edwardschmitz/sigcore-uc/docs/Drawings/sketches/4-20mA-output-loop.png

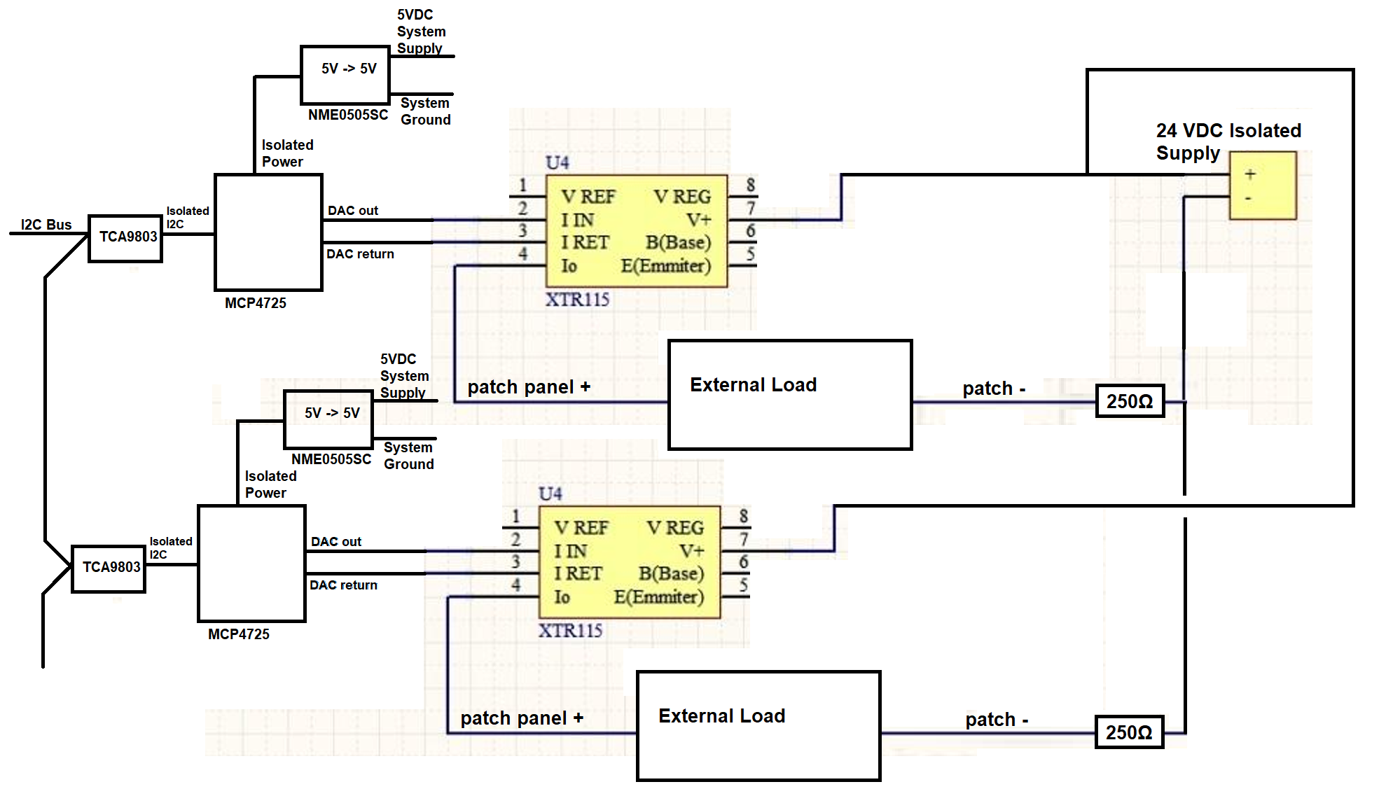
docs/Drawings/sketches/4-20mA-output-loop.png
