edwardschmitz/sigcore-uc/docs/Drawings/sketches/analog-in-conditinoer-select.png

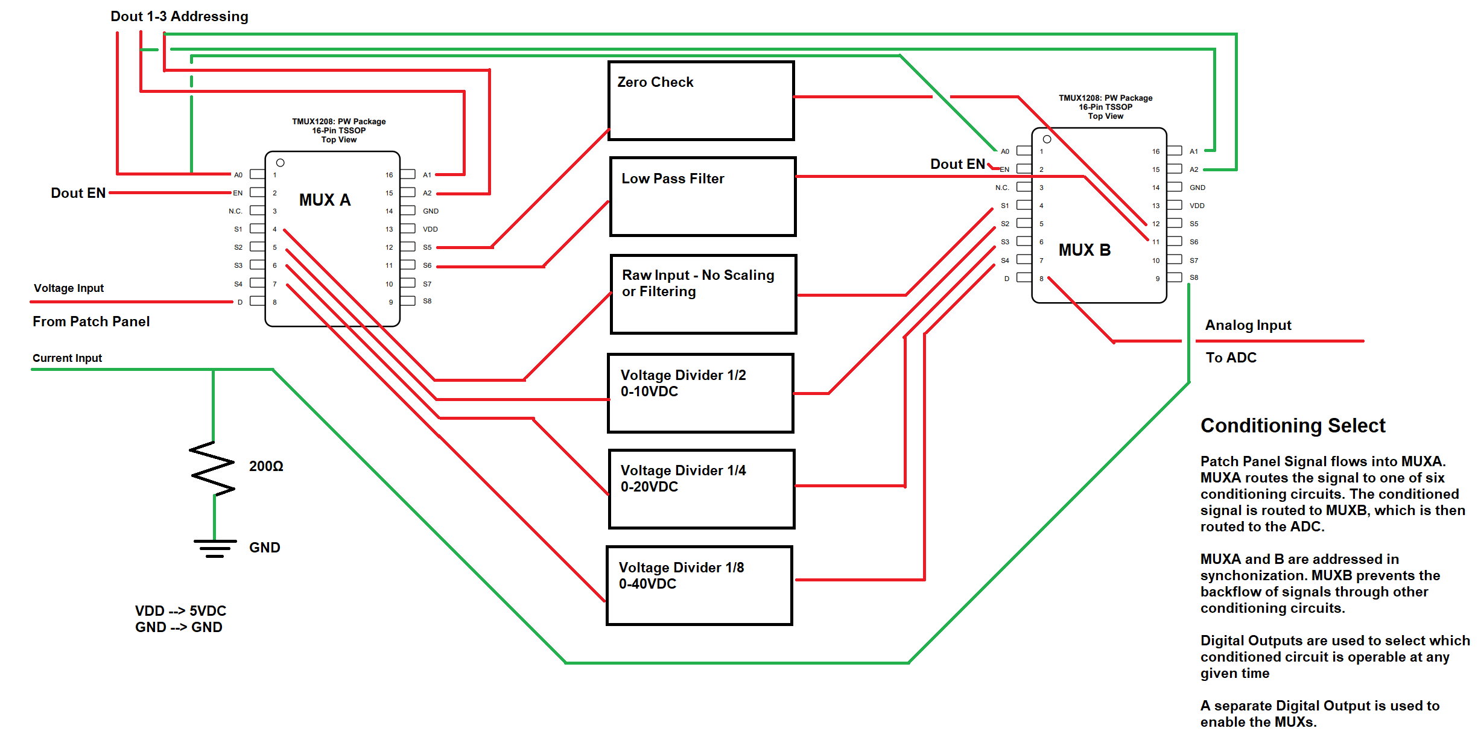
docs/Drawings/sketches/analog-in-conditinoer-select.png
