edwardschmitz/sigcore-uc/docs/Drawings/sketches/current-sensing.png

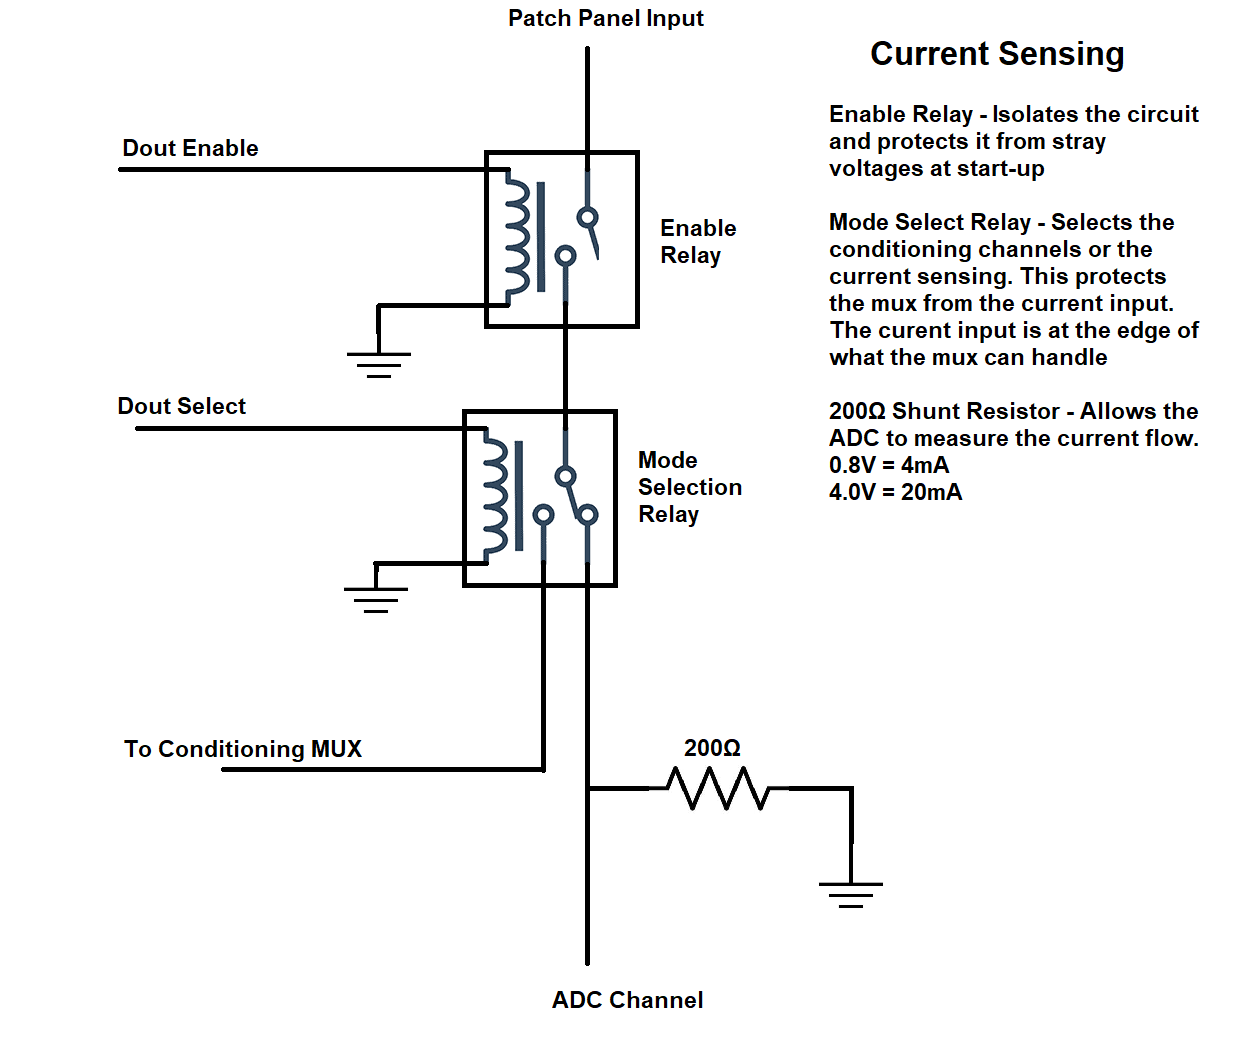
docs/Drawings/sketches/current-sensing.png
