edwardschmitz/sigcore-uc/docs/Drawings/sketches/Relay Driver.png

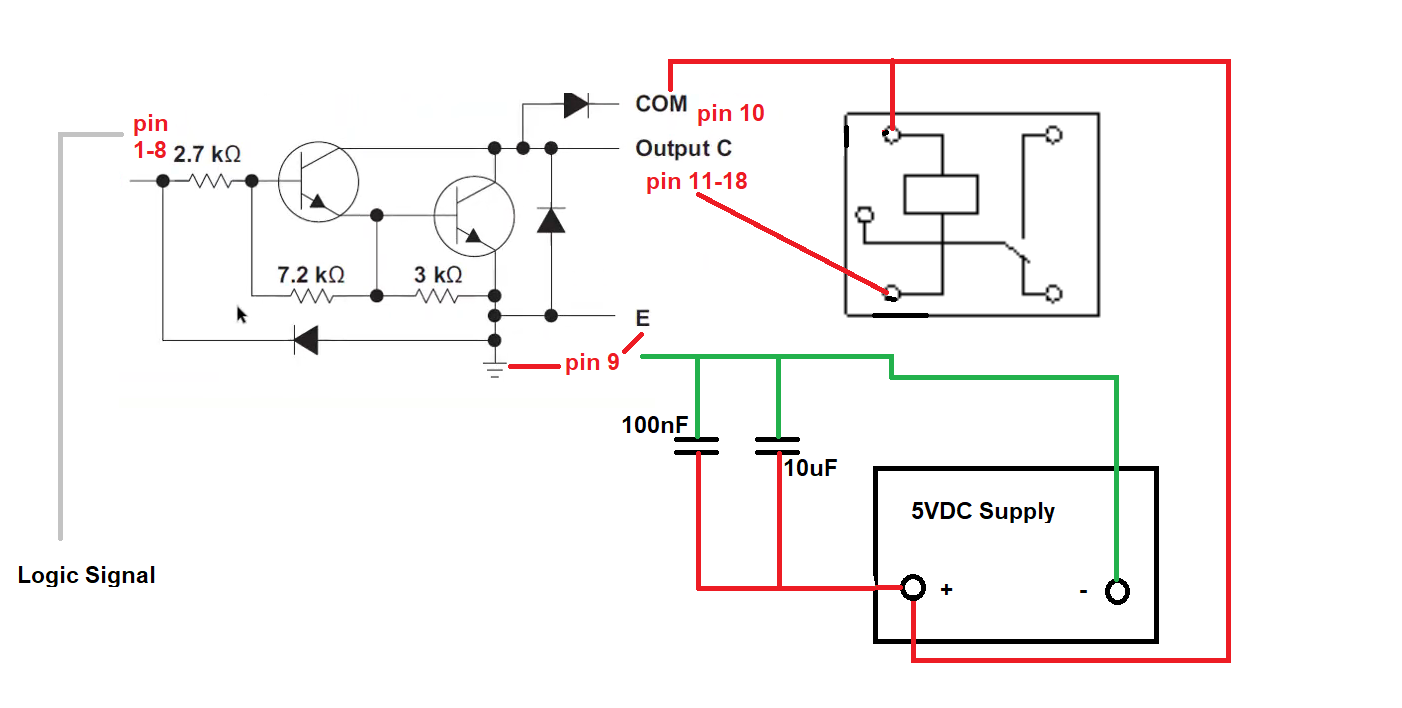
docs/Drawings/sketches/Relay Driver.png
