edwardschmitz/sigcore-uc/docs/Drawings/sketches/relay-circuit.png

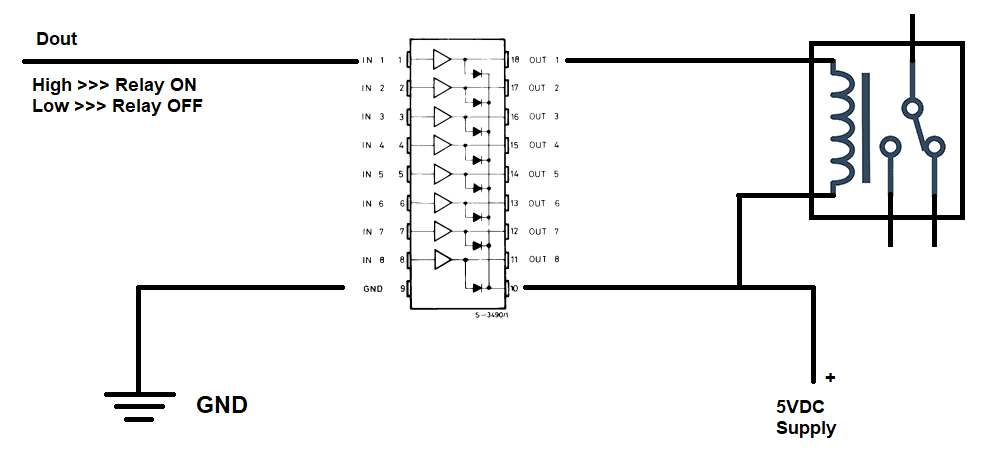
docs/Drawings/sketches/relay-circuit.png
