edwardschmitz/sigcore-uc/docs/Drawings/sketches/universal-analog-output.png

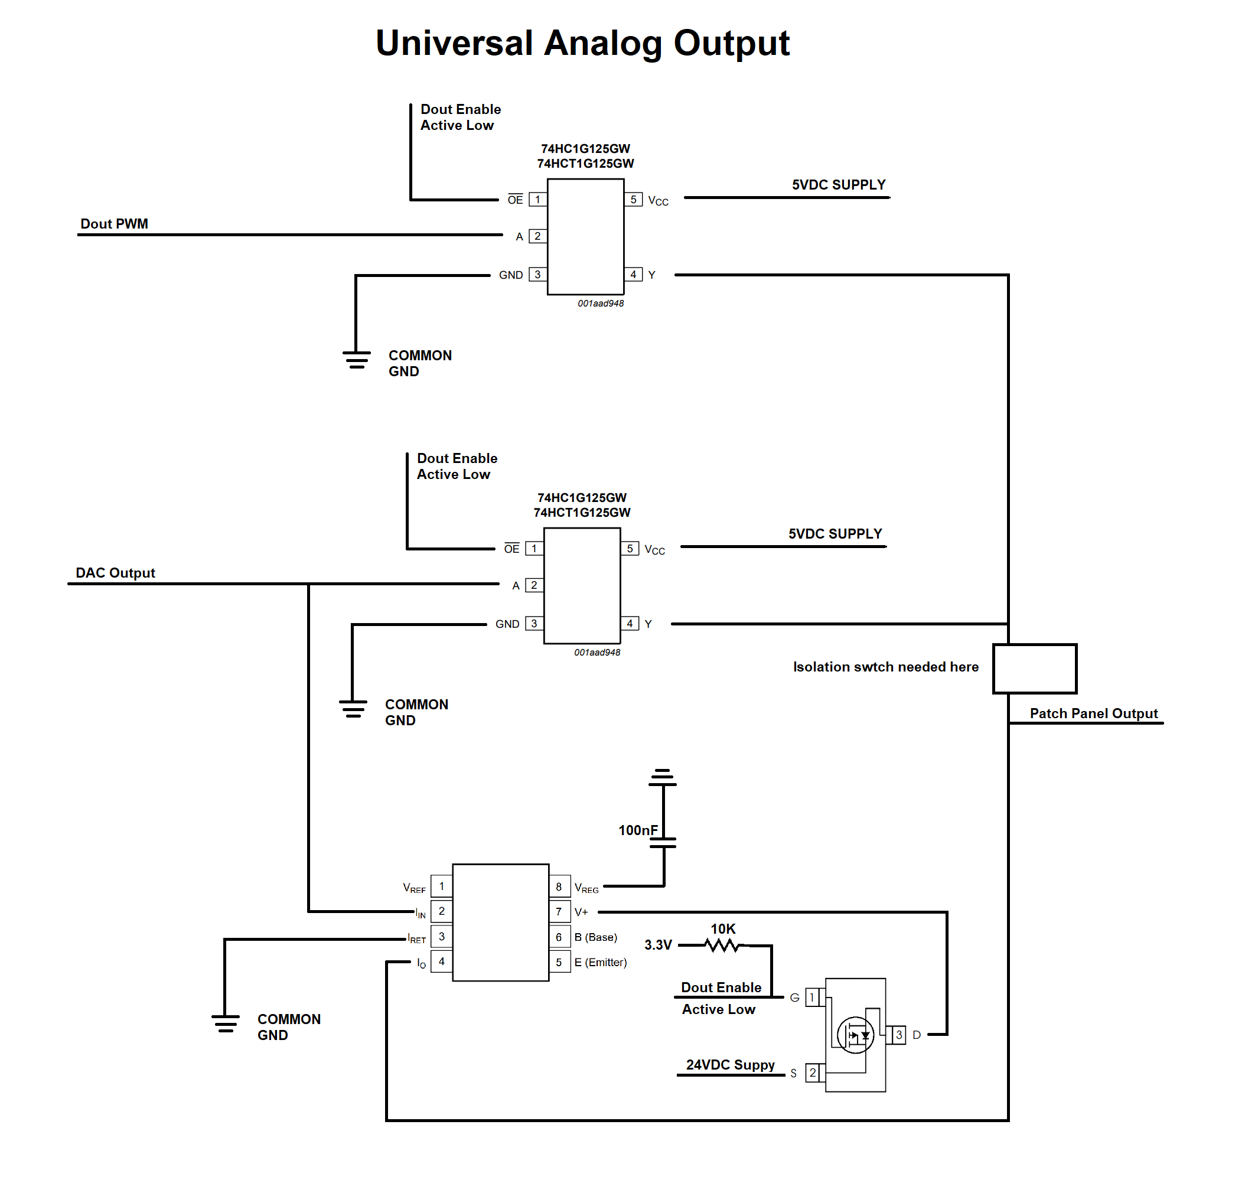
docs/Drawings/sketches/universal-analog-output.png
