edwardschmitz/sigcore-uc/docs/Drawings/sketches/universal-digital-input.png

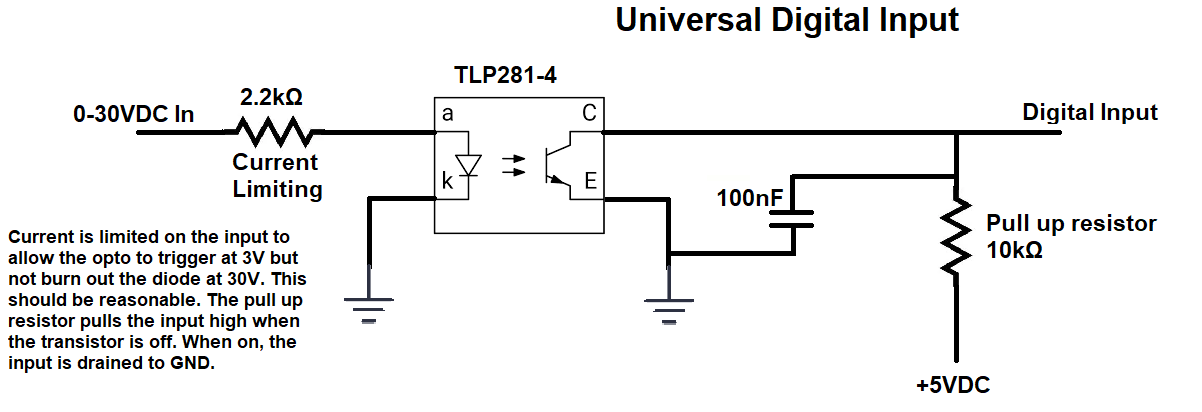
docs/Drawings/sketches/universal-digital-input.png
