edwardschmitz/sigcore-uc/docs/Images/1000008632.jpg

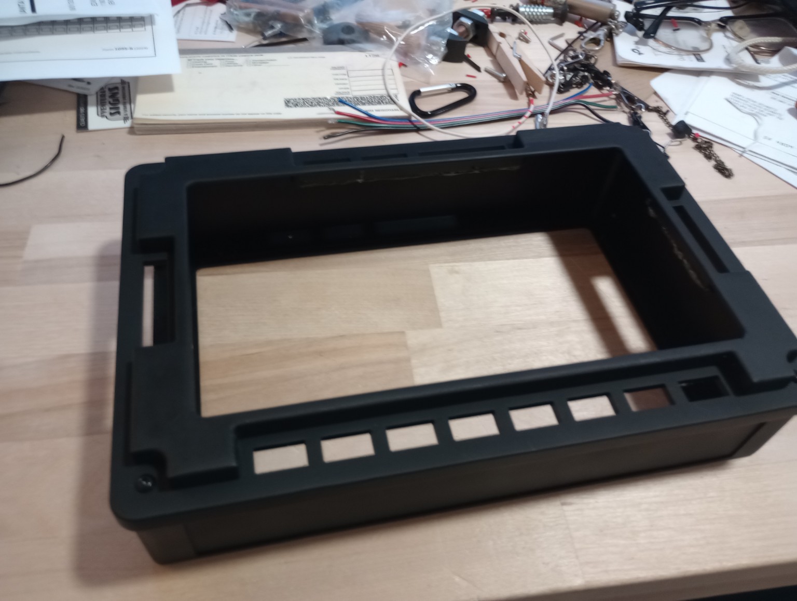
docs/Images/1000008632.jpg
