edwardschmitz/sigcore-uc/docs/Images/1000009032.jpg

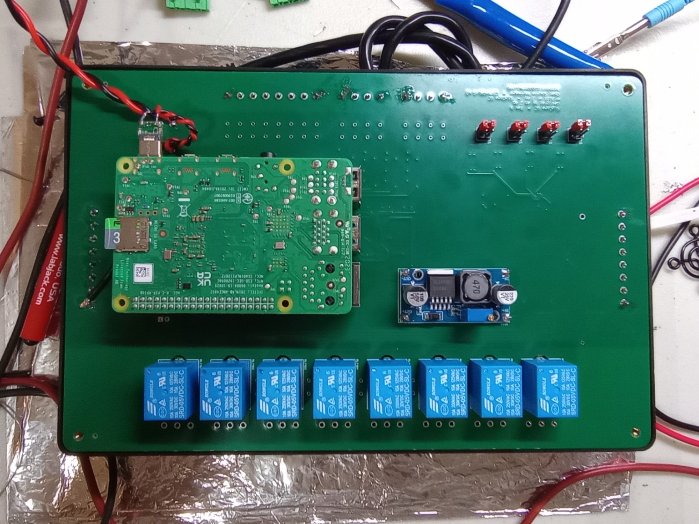
docs/Images/1000009032.jpg
