edwardschmitz/sigcore-uc/docs/Images/1000009033.jpg

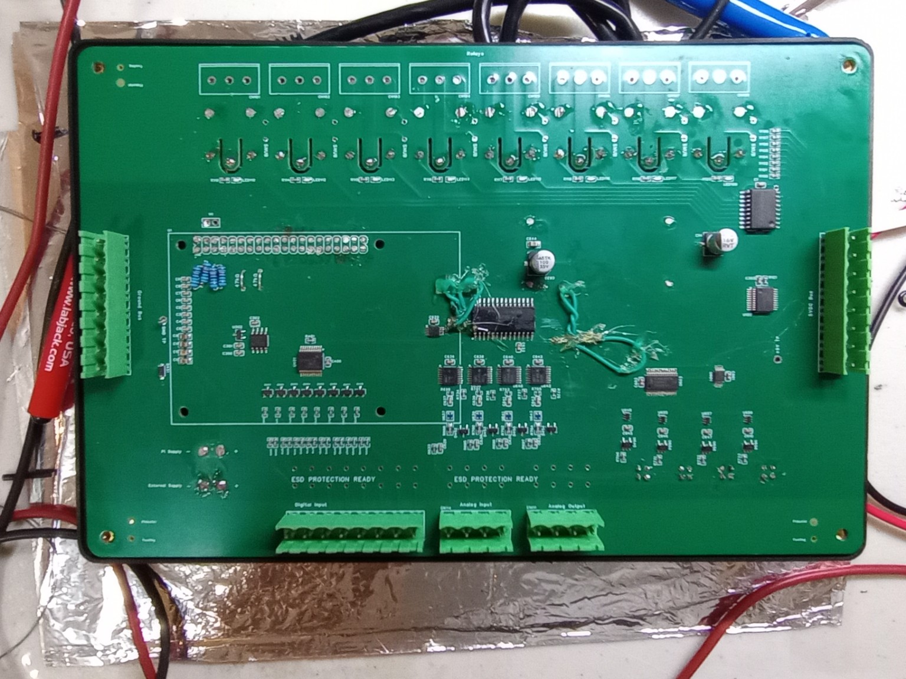
docs/Images/1000009033.jpg
