edwardschmitz/sigcore-uc/docs/Images/abstract-circuit.png

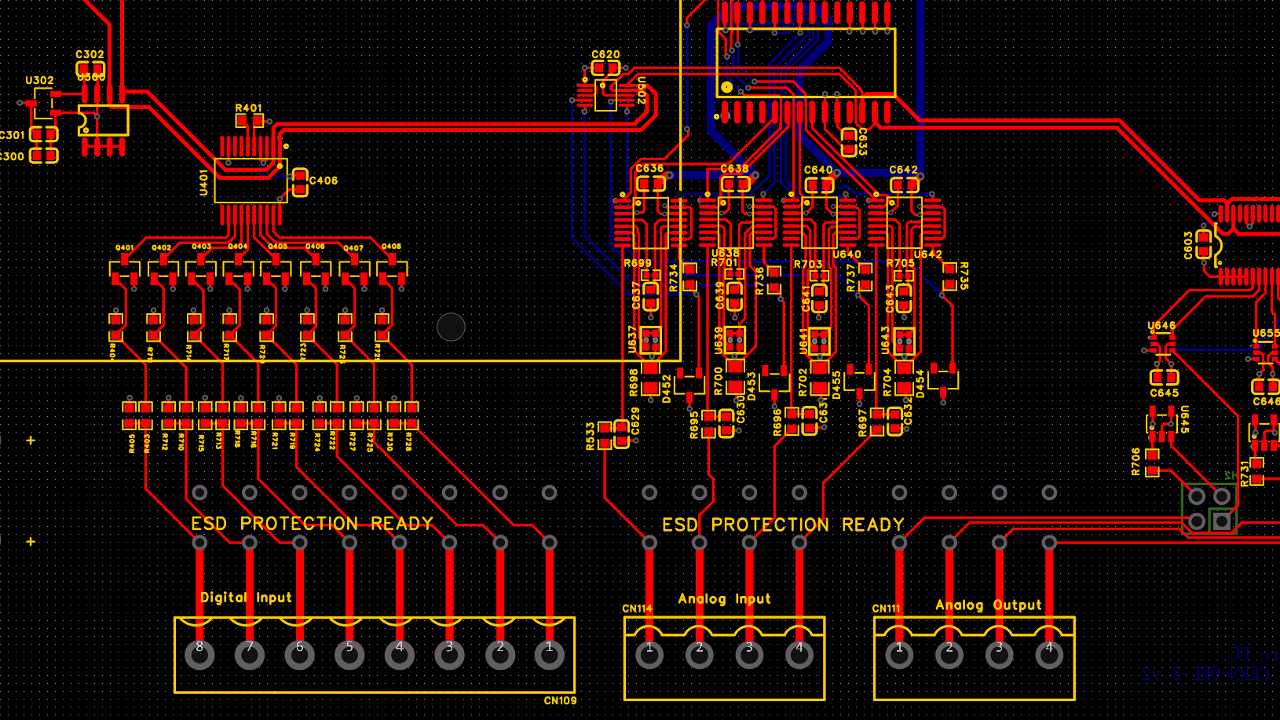
docs/Images/abstract-circuit.png
