edwardschmitz/sigcore-uc/docs/Images/analog-properties.png

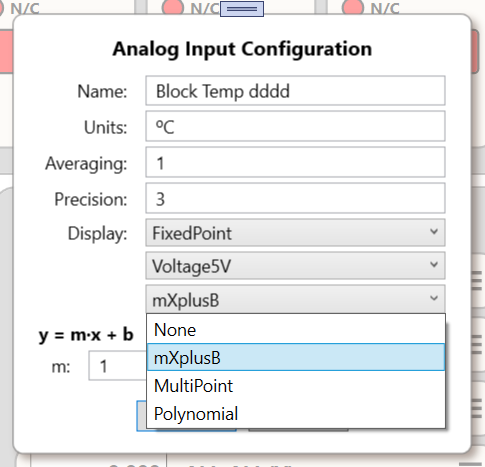
docs/Images/analog-properties.png
