edwardschmitz/sigcore-uc/docs/Images/angle-view.jpg

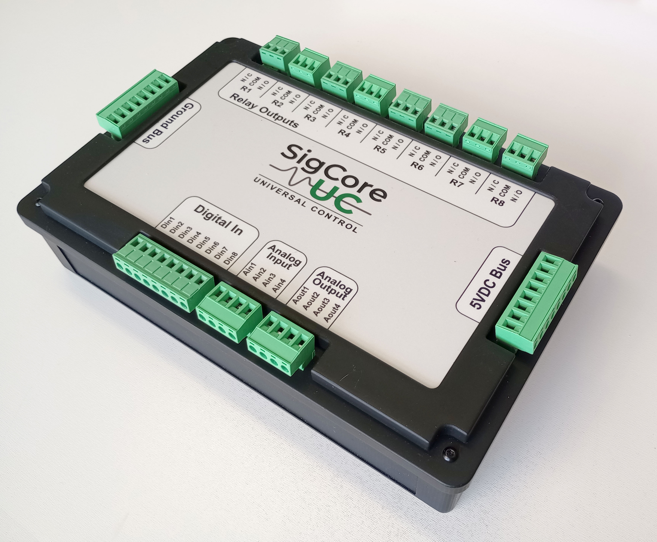
docs/Images/angle-view.jpg
