edwardschmitz/sigcore-uc/docs/Images/Board_v1_2025-Sep-24_08-21-38PM-000_CustomizedView15039400652.png

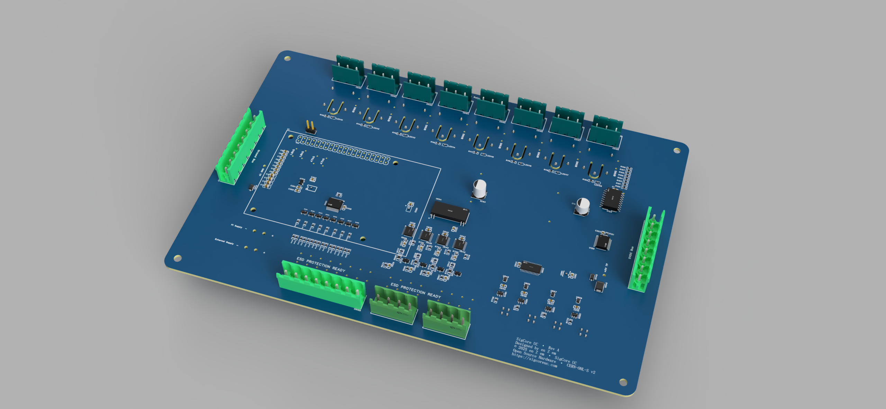
docs/Images/Board_v1_2025-Sep-24_08-21-38PM-000_CustomizedView15039400652.png
