edwardschmitz/sigcore-uc/docs/Images/breakout board.jpg

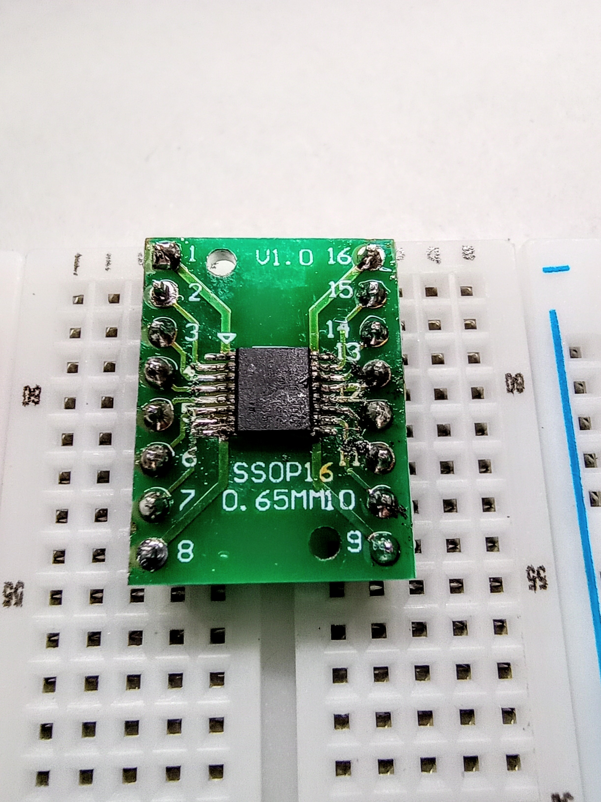
docs/Images/breakout board.jpg
