edwardschmitz/sigcore-uc/docs/Images/circuit-board.png

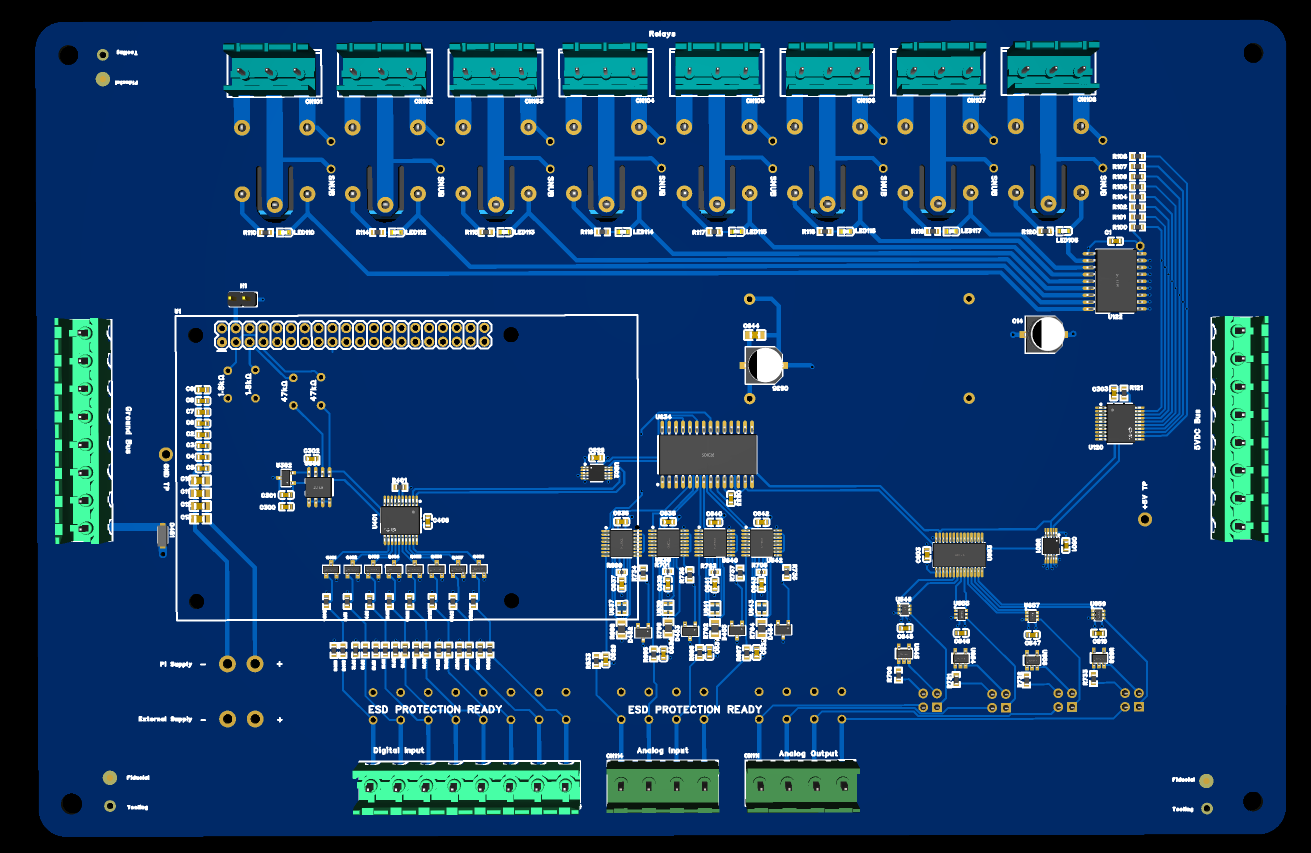
docs/Images/circuit-board.png
