edwardschmitz/sigcore-uc/docs/Images/control-panel-software.png

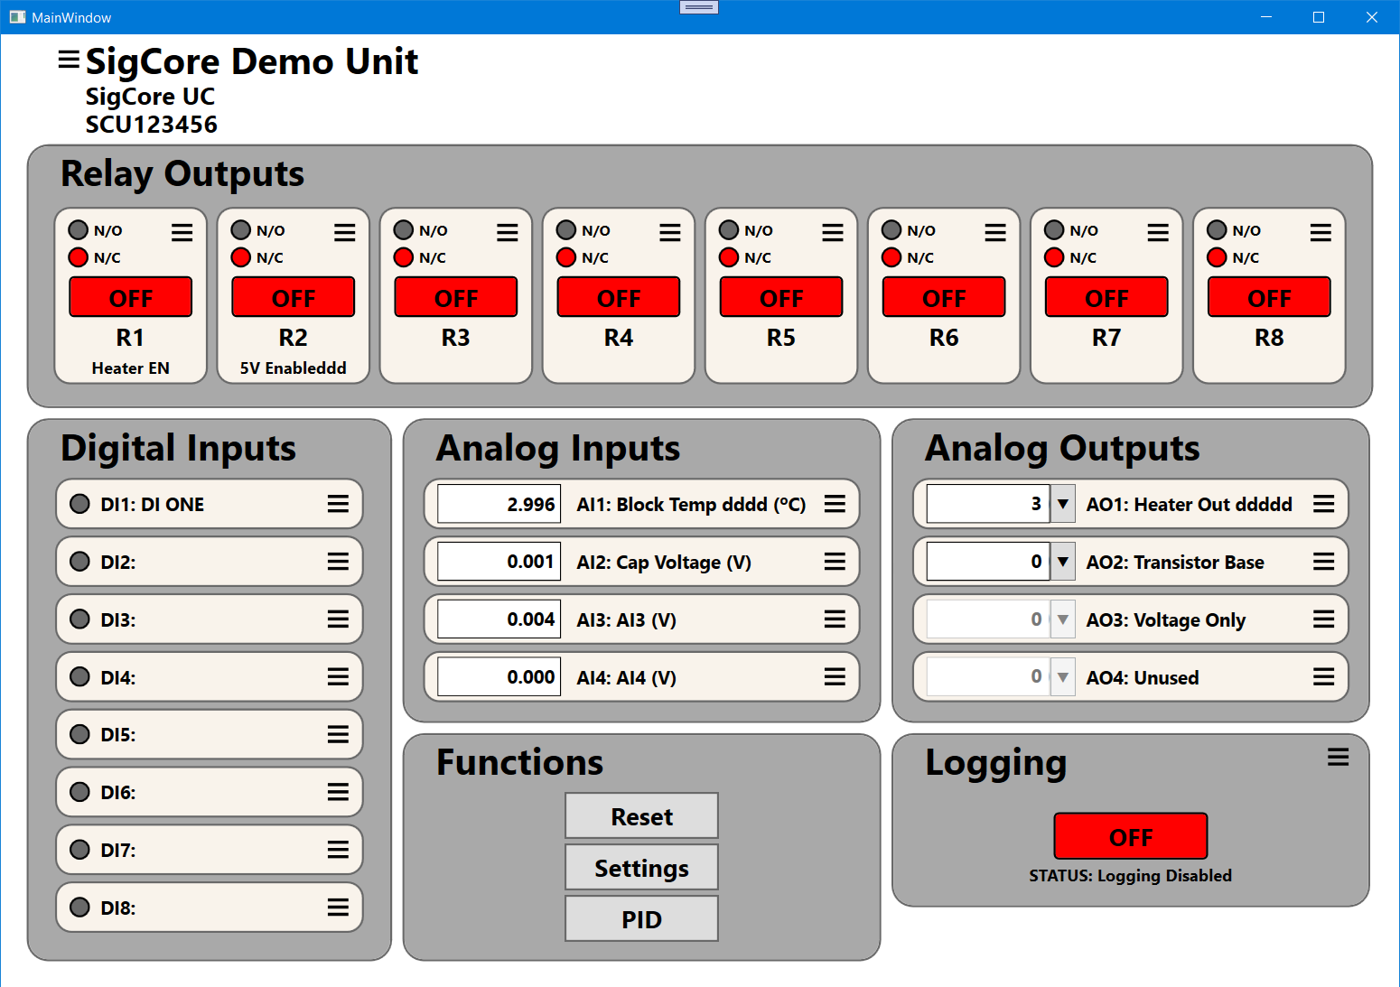
docs/Images/control-panel-software.png
