edwardschmitz/sigcore-uc/docs/Images/enclosure-rendering.png

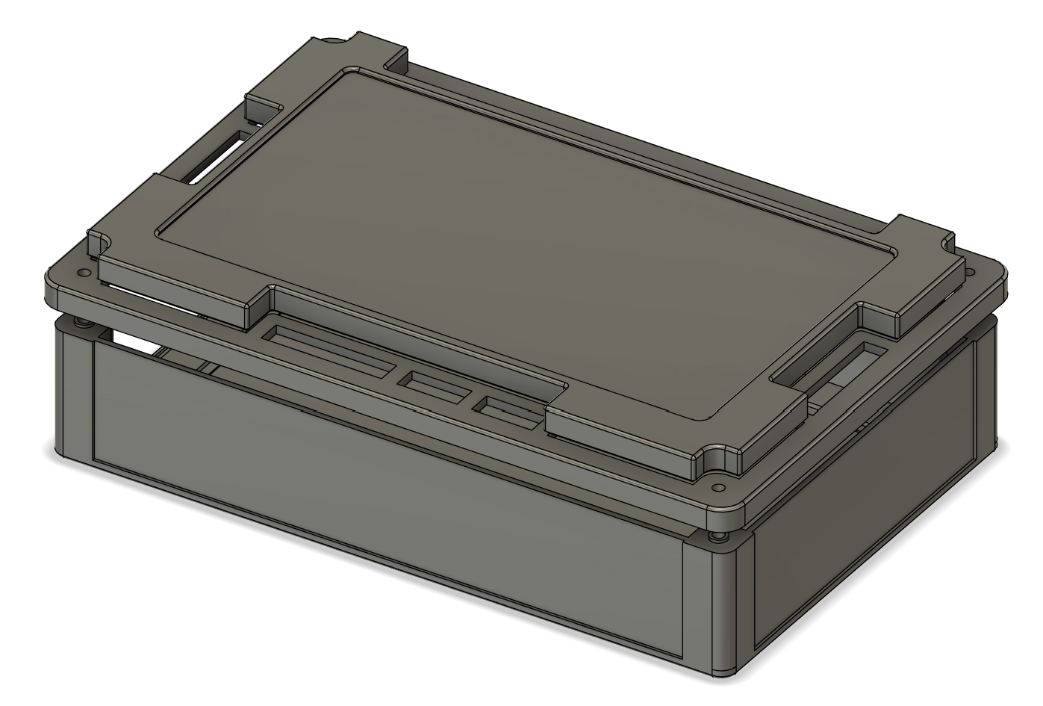
docs/Images/enclosure-rendering.png
