edwardschmitz/sigcore-uc/docs/Images/front-angle.jpg

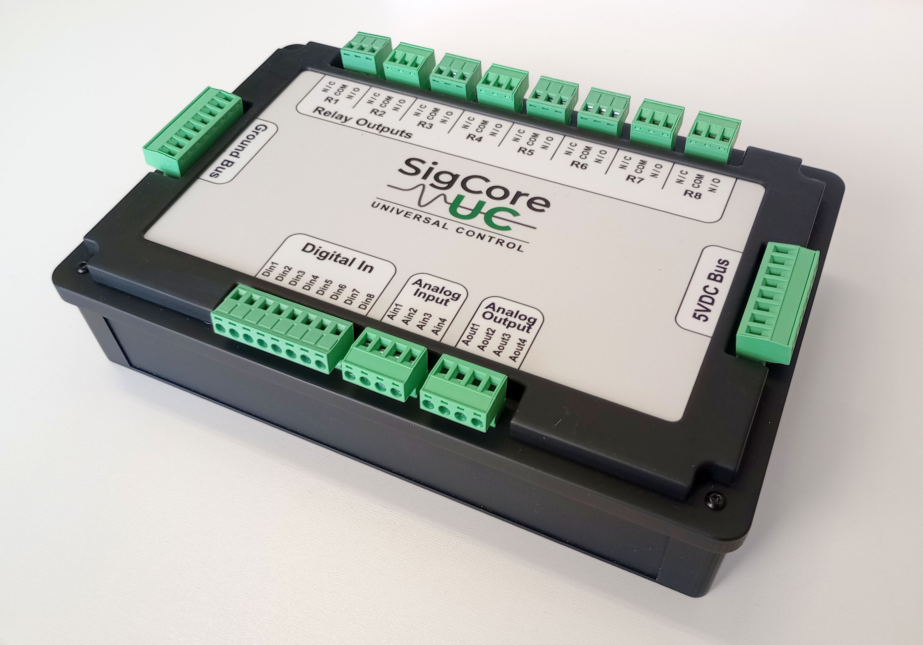
docs/Images/front-angle.jpg
