edwardschmitz/sigcore-uc/docs/Images/front.jpg

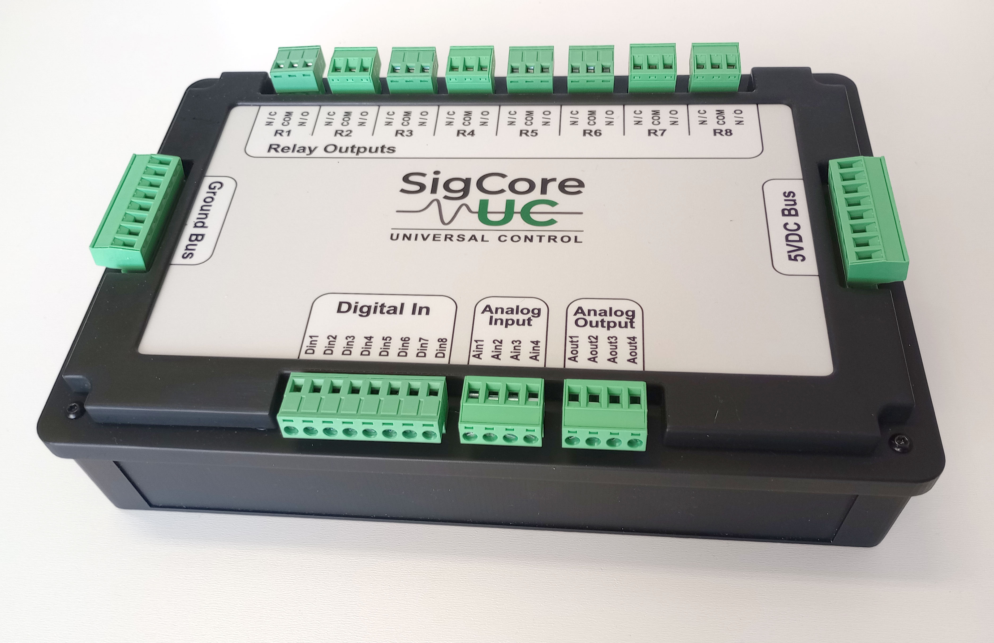
docs/Images/front.jpg
