edwardschmitz/sigcore-uc/docs/Images/hackster-article.jpg

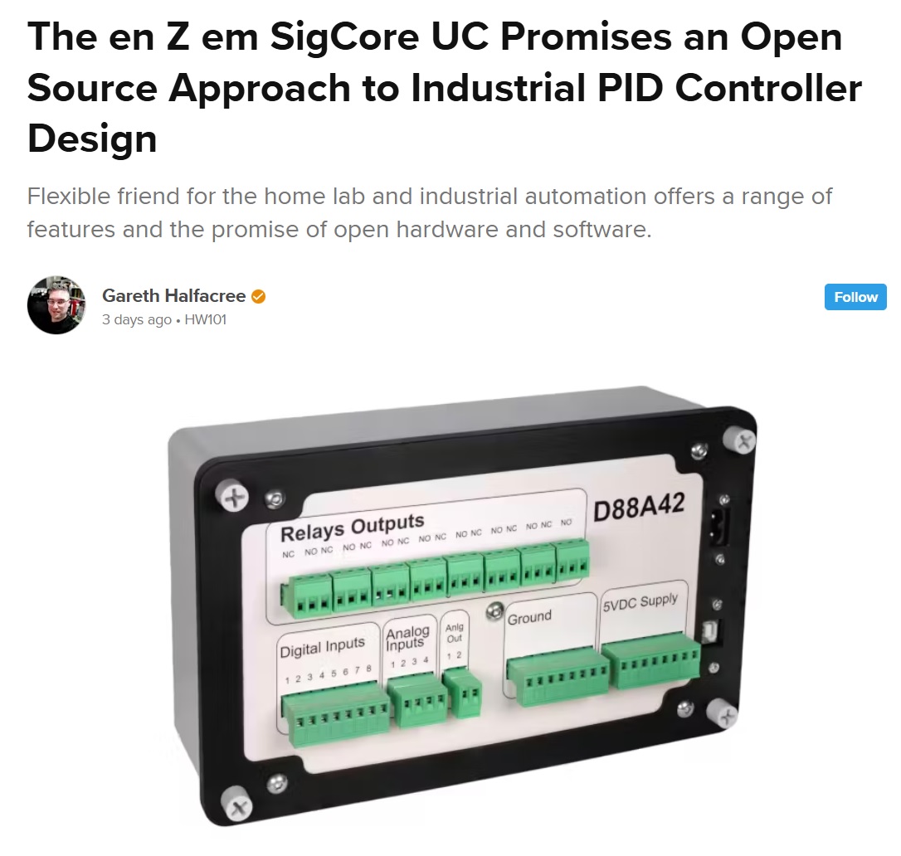
docs/Images/hackster-article.jpg
