edwardschmitz/sigcore-uc/docs/Images/IMG_20250718_141825615.jpg

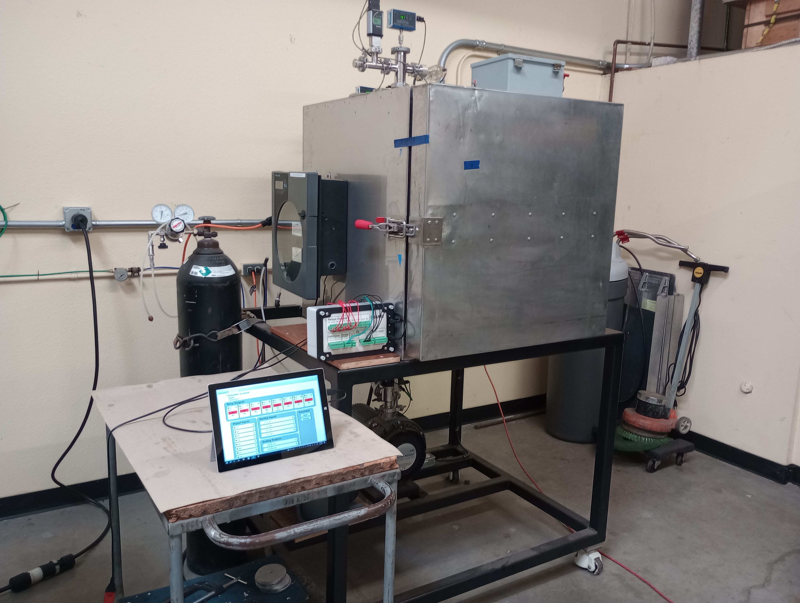
docs/Images/IMG_20250718_141825615.jpg
