edwardschmitz/sigcore-uc/docs/Images/IMG_20250718_141832880.jpg

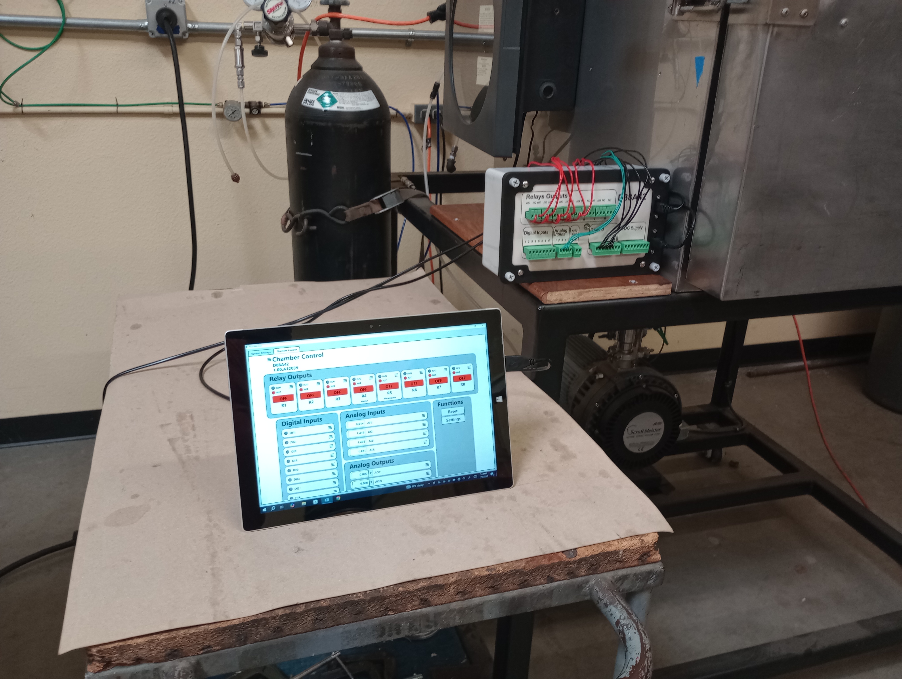
docs/Images/IMG_20250718_141832880.jpg
