edwardschmitz/sigcore-uc/docs/Images/IMG_20250718_141838460.jpg

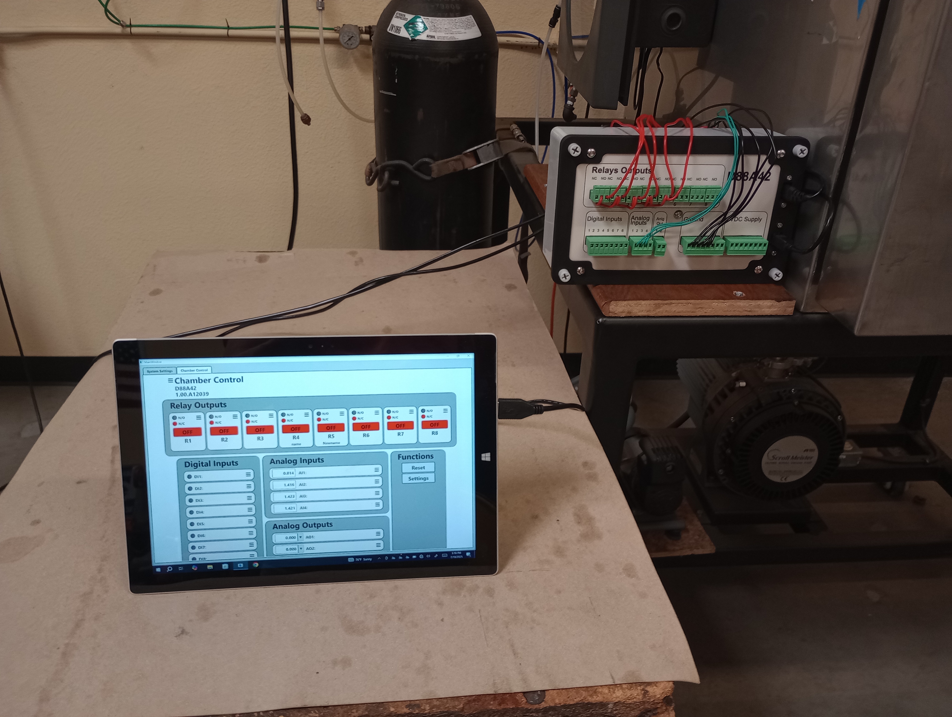
docs/Images/IMG_20250718_141838460.jpg
