edwardschmitz/sigcore-uc/docs/Images/IMG_20250718_141848650.jpg

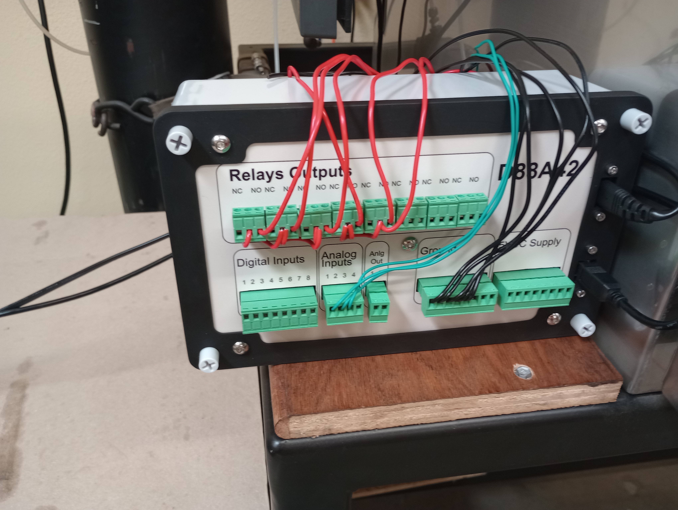
docs/Images/IMG_20250718_141848650.jpg
