edwardschmitz/sigcore-uc/docs/Images/IMG_20250718_141900908.jpg

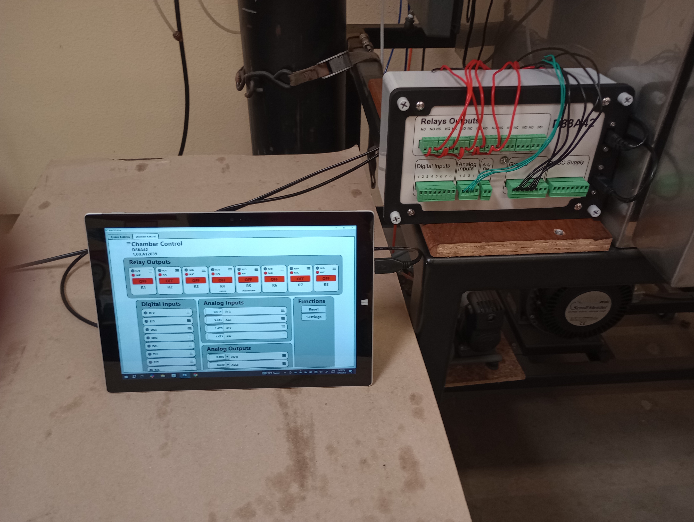
docs/Images/IMG_20250718_141900908.jpg
