edwardschmitz/sigcore-uc/docs/Images/IMG_20250718_143222500.jpg

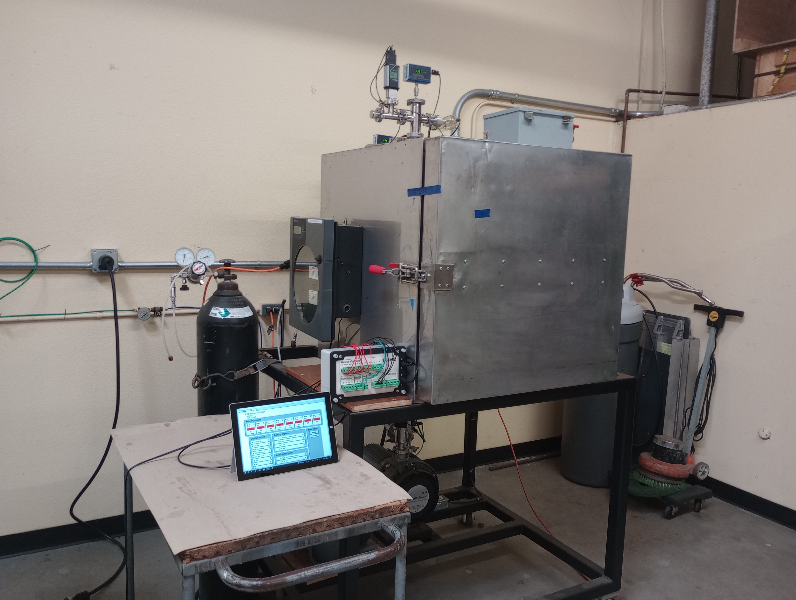
docs/Images/IMG_20250718_143222500.jpg
