edwardschmitz/sigcore-uc/docs/Images/IMG_20250718_143229647.jpg

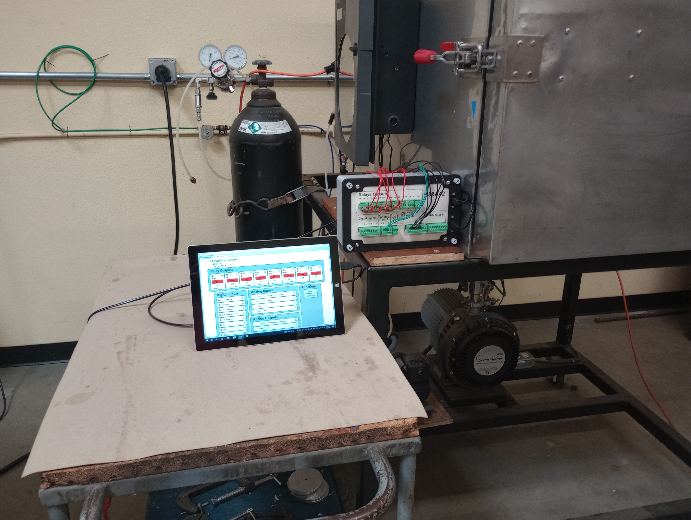
docs/Images/IMG_20250718_143229647.jpg
