edwardschmitz/sigcore-uc/docs/Images/IMG_20250718_143235979.jpg

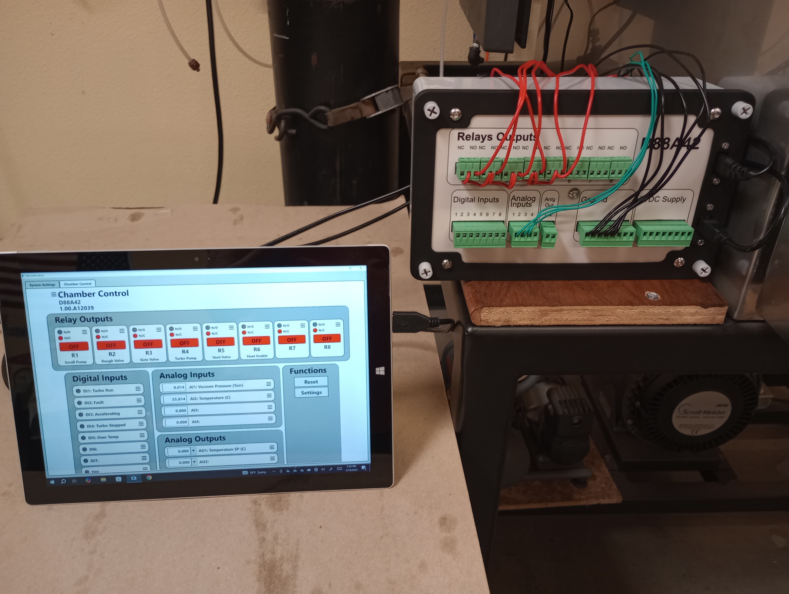
docs/Images/IMG_20250718_143235979.jpg
