edwardschmitz/sigcore-uc/docs/Images/IMG_20250718_143255635.jpg

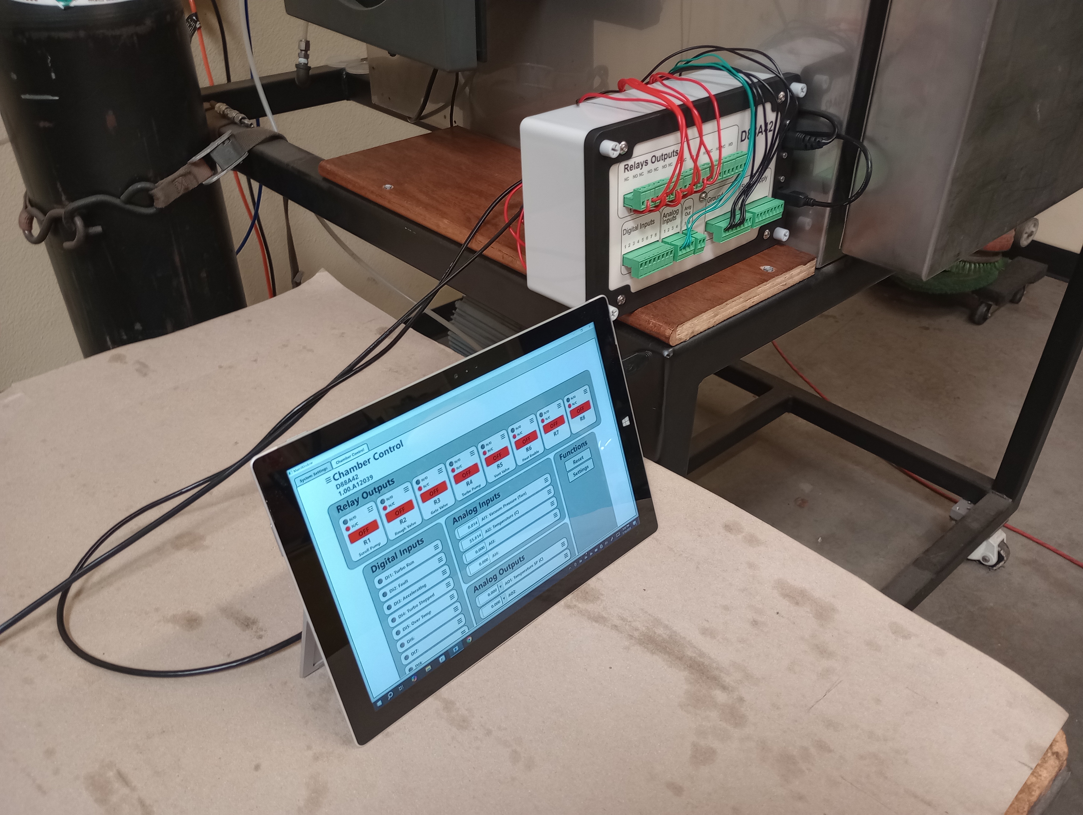
docs/Images/IMG_20250718_143255635.jpg
