edwardschmitz/sigcore-uc/docs/Images/IMG_20250718_143305820.jpg

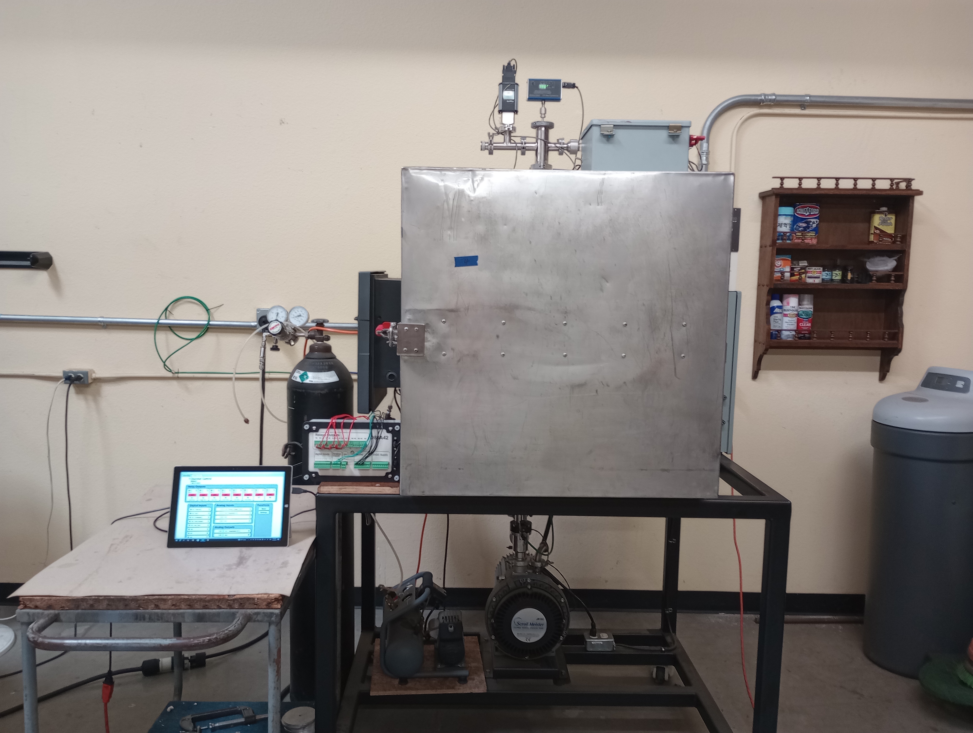
docs/Images/IMG_20250718_143305820.jpg
