edwardschmitz/sigcore-uc/docs/Images/IMG_20250718_143310509.jpg

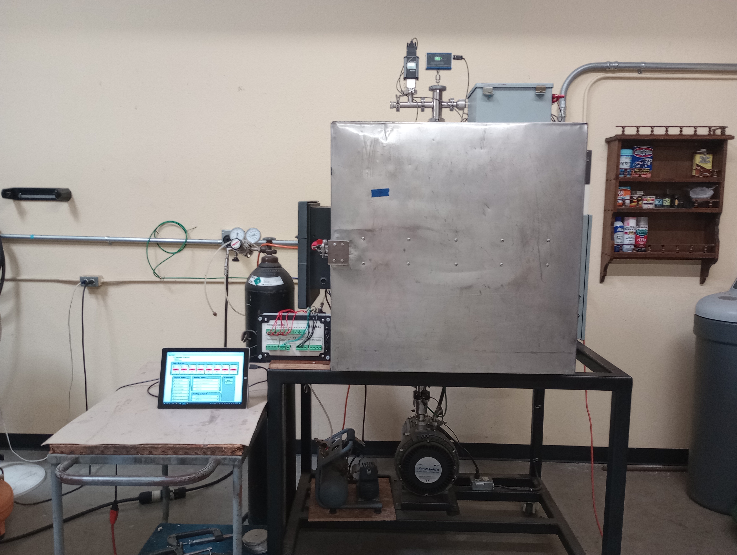
docs/Images/IMG_20250718_143310509.jpg
