edwardschmitz/sigcore-uc/docs/Images/IMG_20250803_220448067.jpg

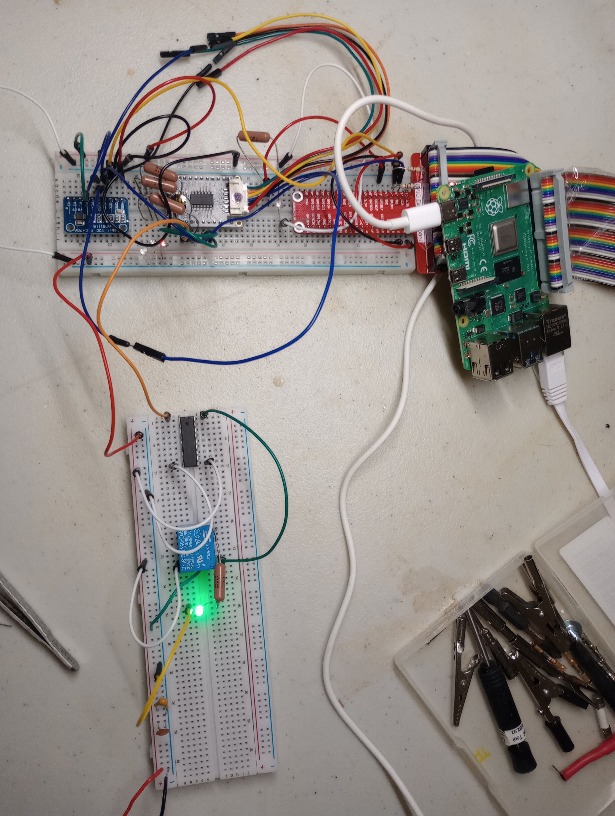
docs/Images/IMG_20250803_220448067.jpg
