edwardschmitz/sigcore-uc/docs/Images/IMG_20250916_191023040.jpg

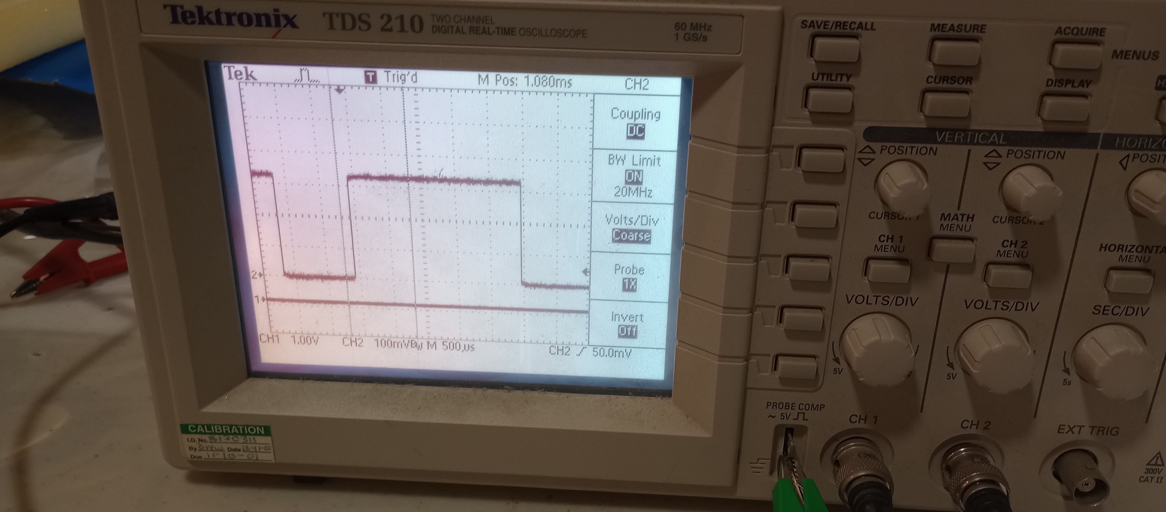
docs/Images/IMG_20250916_191023040.jpg
