edwardschmitz/sigcore-uc/docs/Images/IMG_20250918_153733241~2.jpg

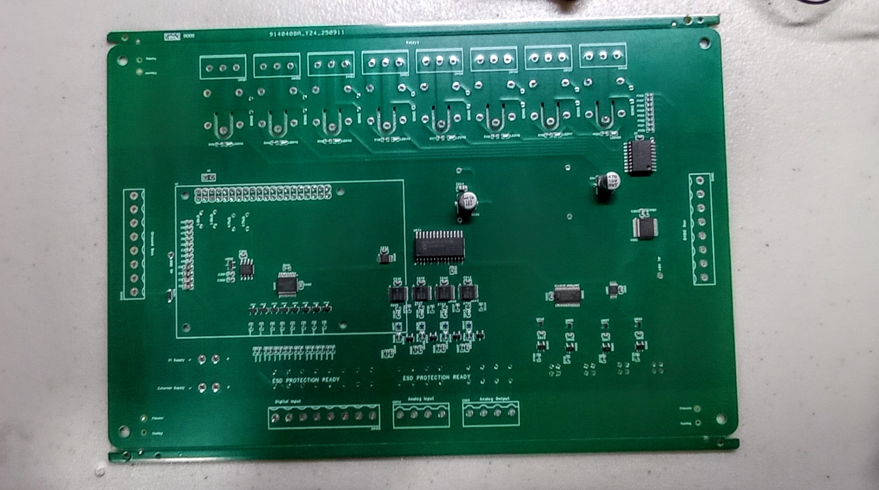
docs/Images/IMG_20250918_153733241~2.jpg
