edwardschmitz/sigcore-uc/docs/Images/led-on.jpg

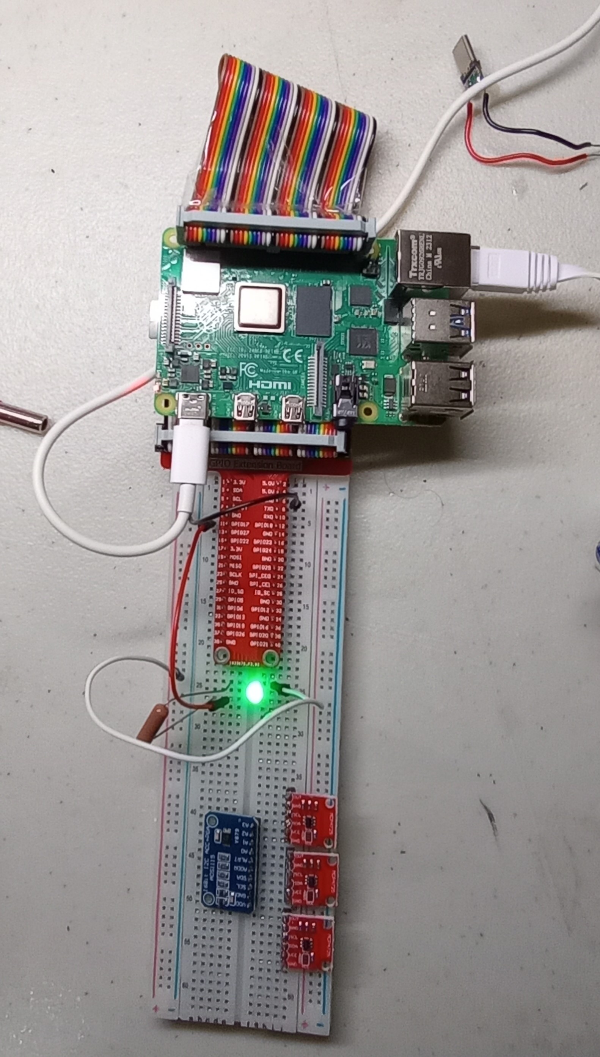
docs/Images/led-on.jpg
