edwardschmitz/sigcore-uc/docs/Images/media2.jpg

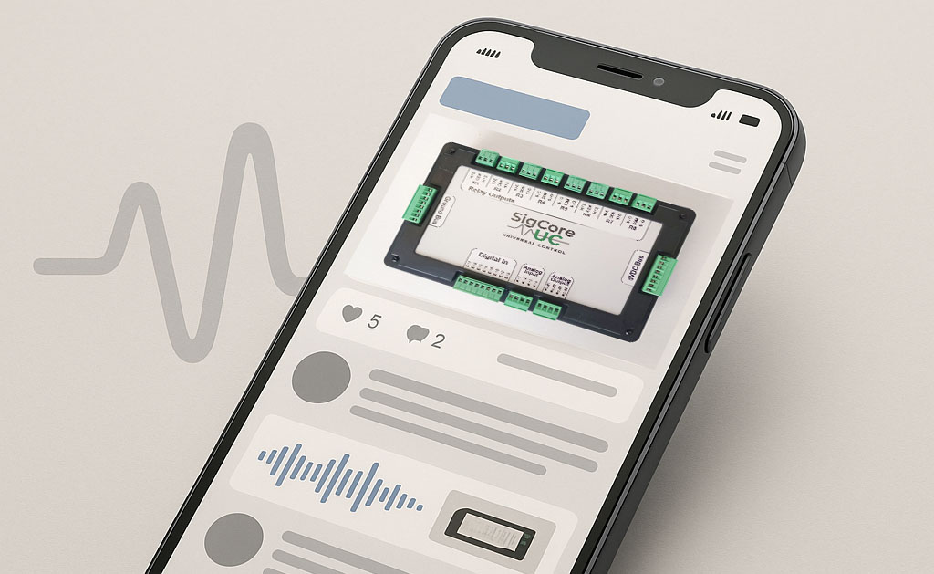
docs/Images/media2.jpg
