edwardschmitz/sigcore-uc/docs/Images/media.jpg

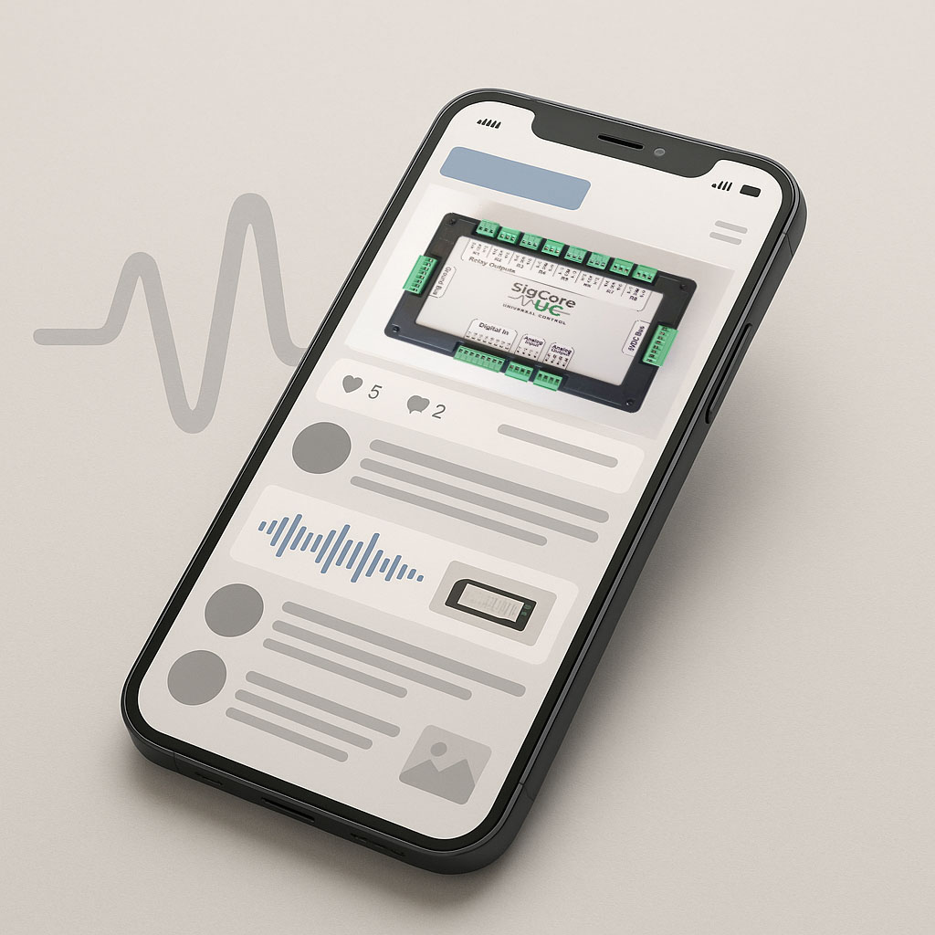
docs/Images/media.jpg
