edwardschmitz/sigcore-uc/docs/Images/mockup/circuit-board-topside.png

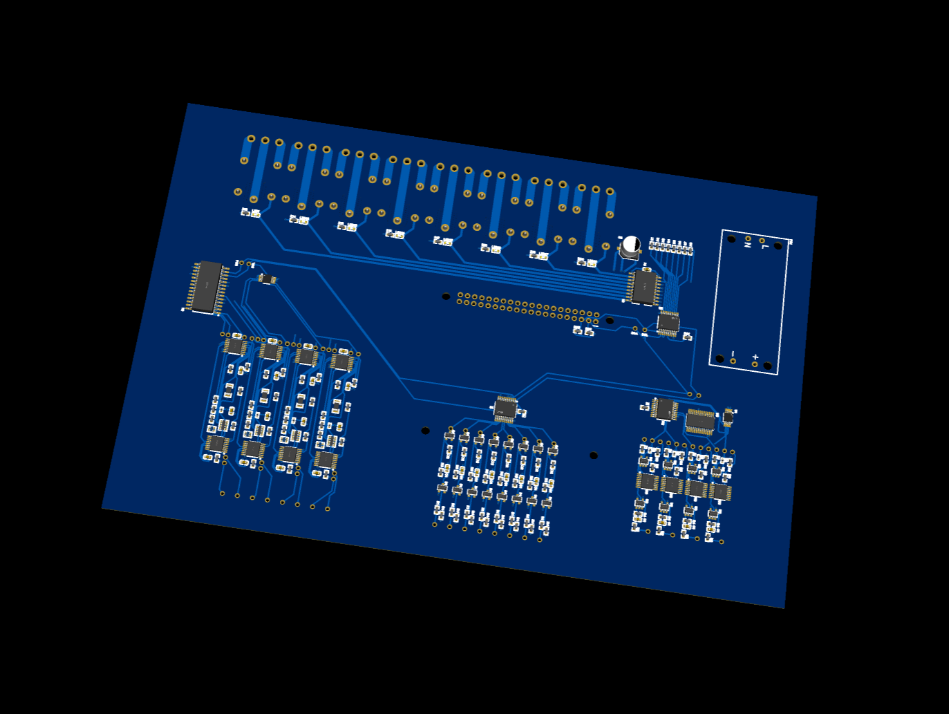
docs/Images/mockup/circuit-board-topside.png
