edwardschmitz/sigcore-uc/docs/Images/mockup/circuit-board-underside.png

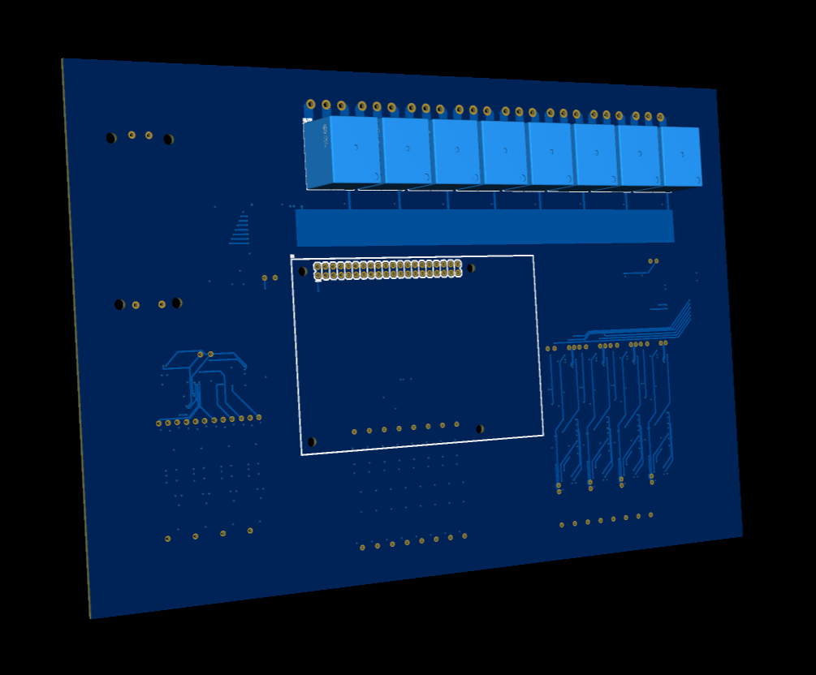
docs/Images/mockup/circuit-board-underside.png
