edwardschmitz/sigcore-uc/docs/Images/mockup/Enclosure_2025-Aug-25_02-53-01AM-000_CustomizedView13724732678.png

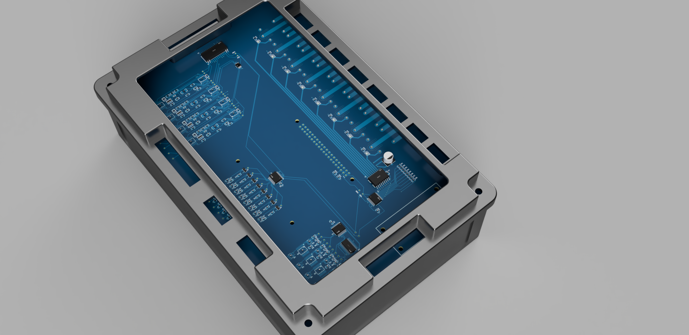
docs/Images/mockup/Enclosure_2025-Aug-25_02-53-01AM-000_CustomizedView13724732678.png
