edwardschmitz/sigcore-uc/docs/Images/mockup/Enclosure_2025-Aug-25_03-08-08AM-000_CustomizedView11488279173.png

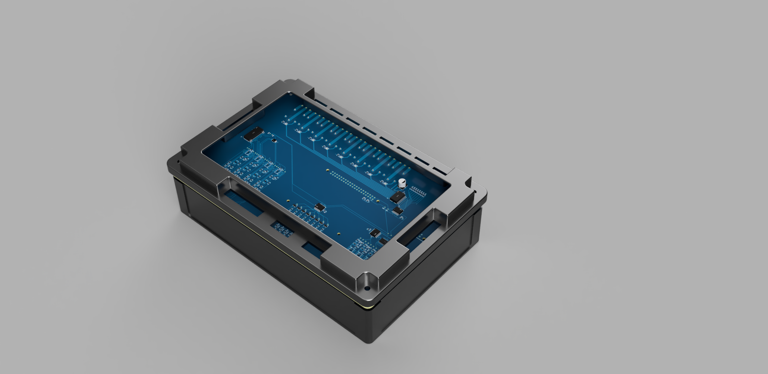
docs/Images/mockup/Enclosure_2025-Aug-25_03-08-08AM-000_CustomizedView11488279173.png
