edwardschmitz/sigcore-uc/docs/Images/mockup/Enclosure_2025-Aug-25_04-47-51AM-000_CustomizedView7637579343.jpg

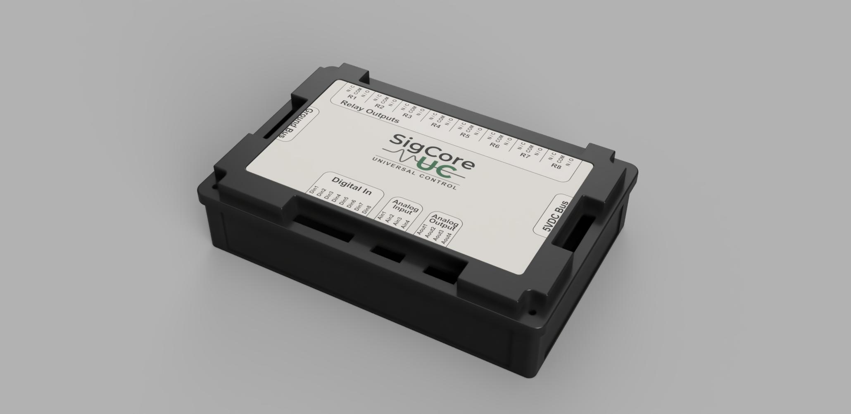
docs/Images/mockup/Enclosure_2025-Aug-25_04-47-51AM-000_CustomizedView7637579343.jpg
