edwardschmitz/sigcore-uc/docs/Images/mockup/trash/IMG_20250812_160700896.jpg

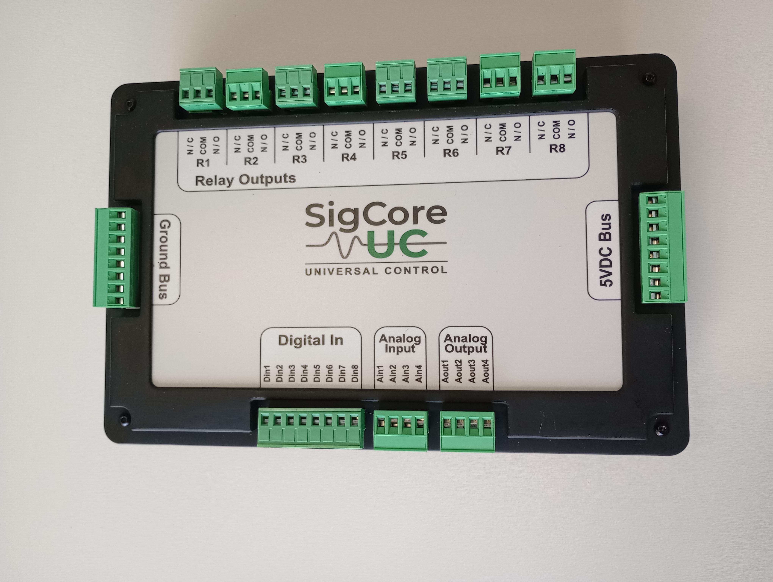
docs/Images/mockup/trash/IMG_20250812_160700896.jpg
