edwardschmitz/sigcore-uc/docs/Images/mockup/trash/IMG_20250812_161103931.jpg

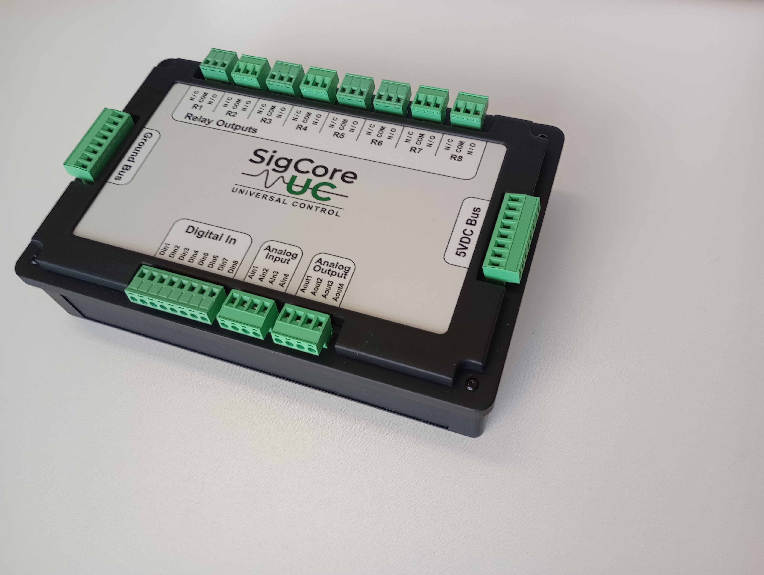
docs/Images/mockup/trash/IMG_20250812_161103931.jpg
