edwardschmitz/sigcore-uc/docs/Images/mockup/trash/IMG_20250812_161157923.jpg

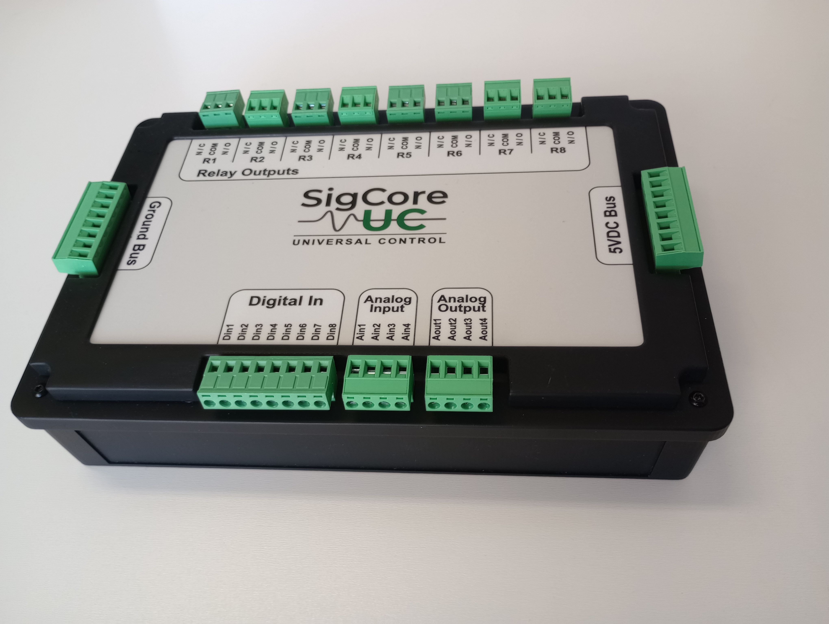
docs/Images/mockup/trash/IMG_20250812_161157923.jpg
