edwardschmitz/sigcore-uc/docs/Images/mockup/trash/IMG_20250812_161208434.jpg

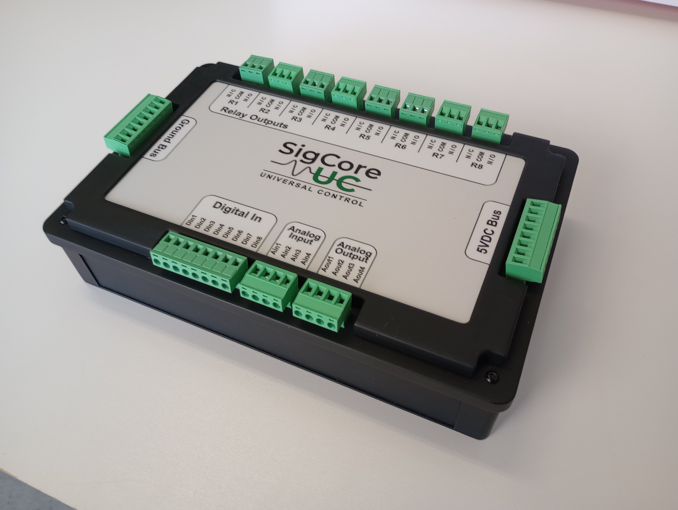
docs/Images/mockup/trash/IMG_20250812_161208434.jpg
