edwardschmitz/sigcore-uc/docs/Images/mockup/trash/IMG_20250812_161233433.jpg

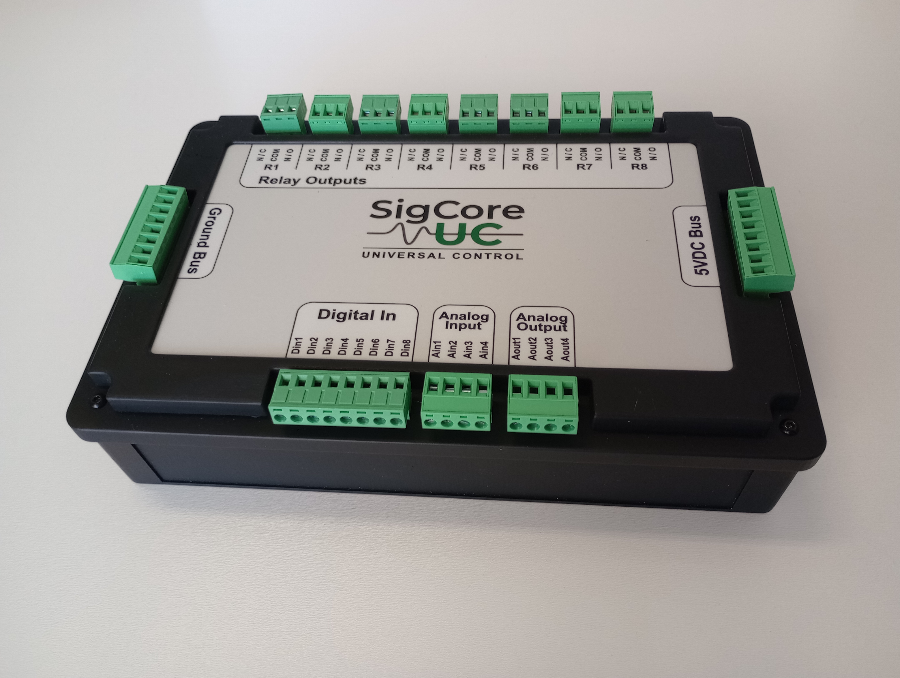
docs/Images/mockup/trash/IMG_20250812_161233433.jpg
