edwardschmitz/sigcore-uc/docs/Images/mockup/trash/IMG_20250812_161237548.jpg

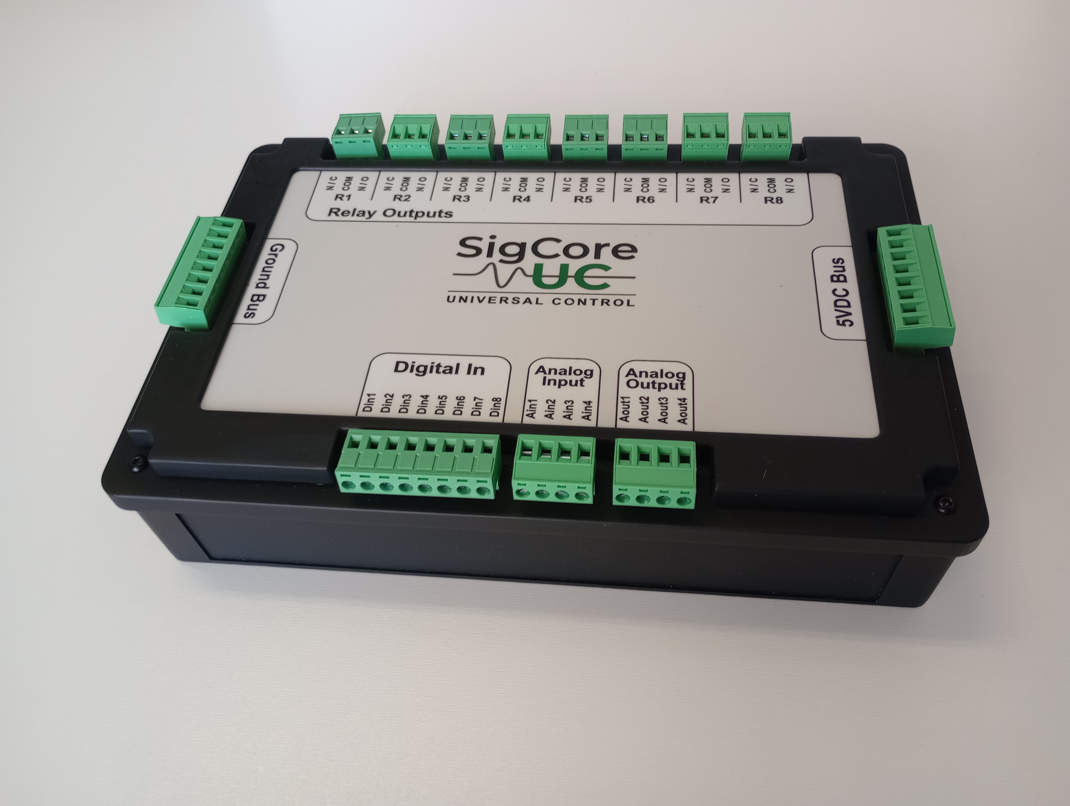
docs/Images/mockup/trash/IMG_20250812_161237548.jpg
