edwardschmitz/sigcore-uc/docs/Images/mockup/trash/IMG_20250812_161326776.jpg

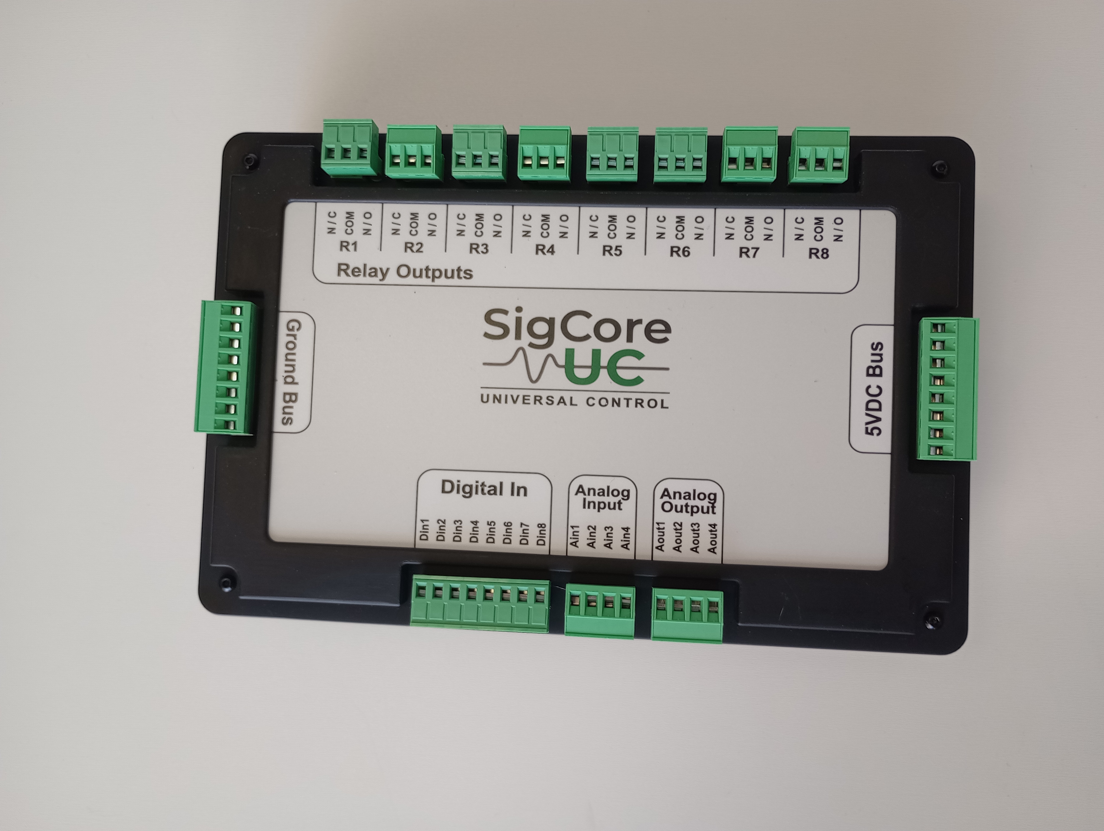
docs/Images/mockup/trash/IMG_20250812_161326776.jpg
