edwardschmitz/sigcore-uc/docs/Images/press-sheet-preview.png

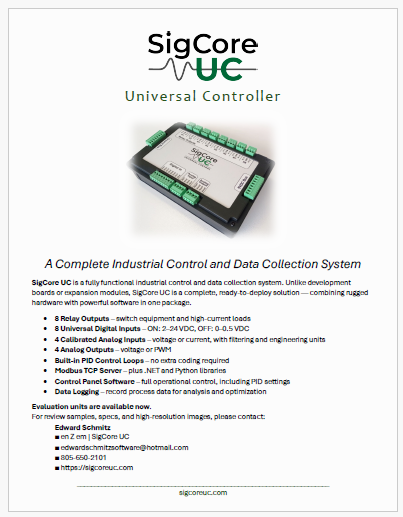
docs/Images/press-sheet-preview.png
