edwardschmitz/sigcore-uc/docs/Images/press.jpg

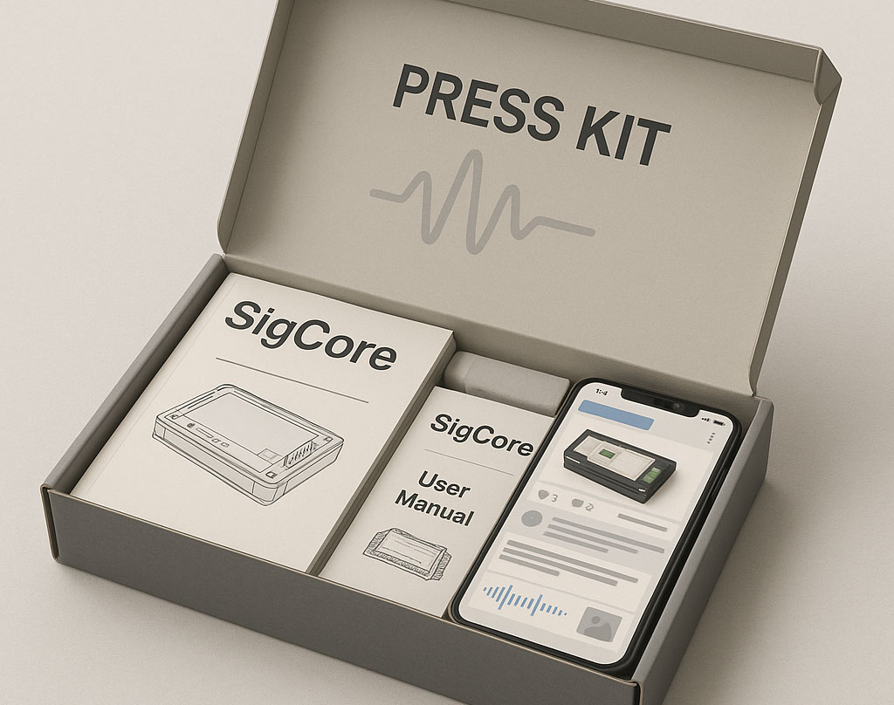
docs/Images/press.jpg
