edwardschmitz/sigcore-uc/docs/Images/prototype/circuit-board-lower.jpg

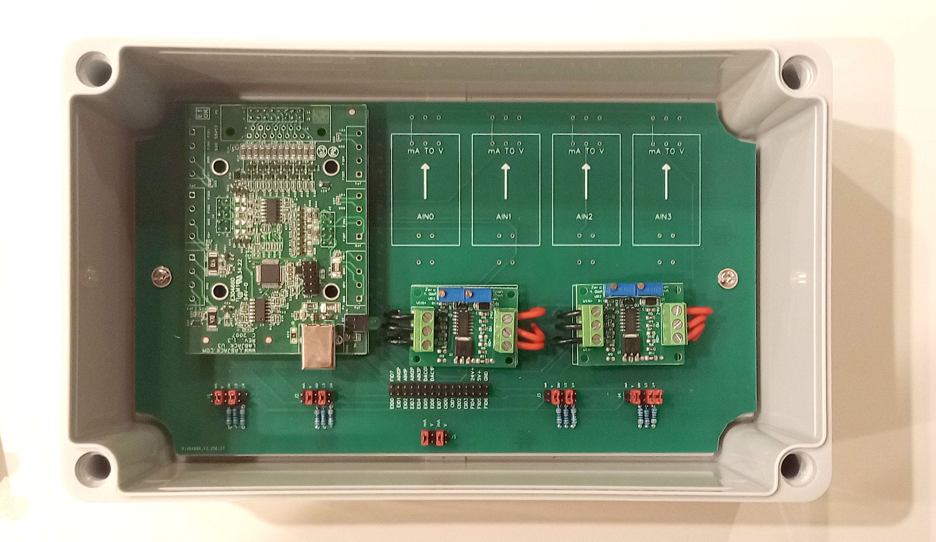
docs/Images/prototype/circuit-board-lower.jpg
