edwardschmitz/sigcore-uc/docs/Images/prototype/circuit-board-upper.jpg

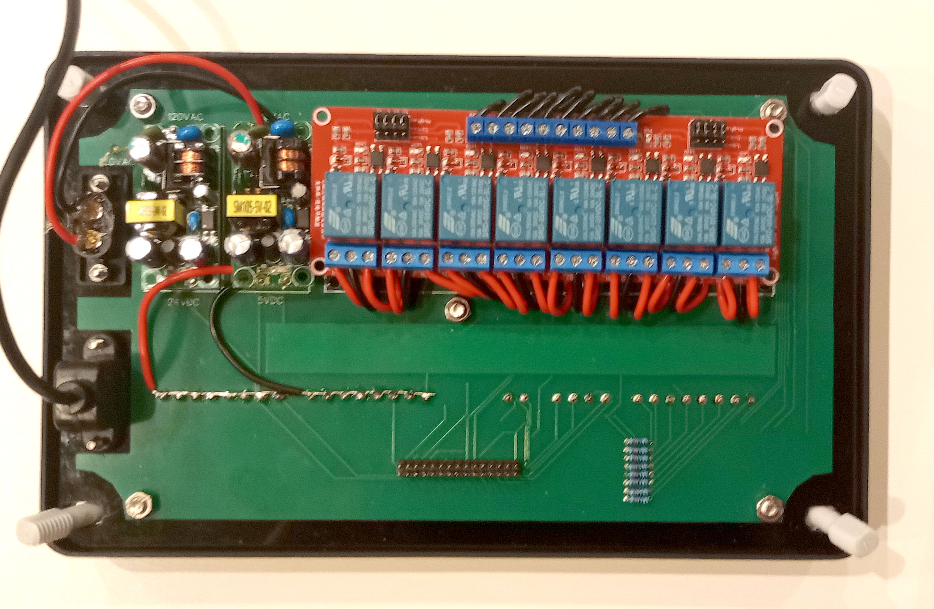
docs/Images/prototype/circuit-board-upper.jpg
