edwardschmitz/sigcore-uc/docs/Images/top-view.jpg

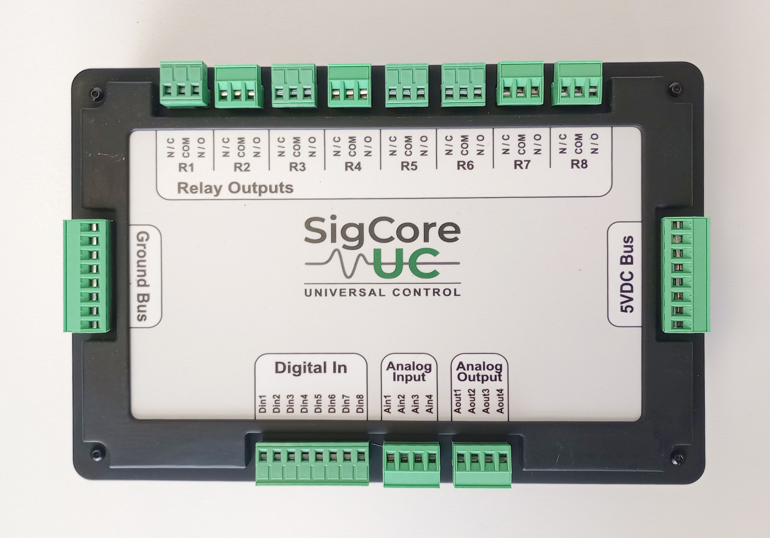
docs/Images/top-view.jpg
