edwardschmitz/sigcore-uc/docs/Renderings/Board_v1_2025-Aug-29_05-47-25AM-000_CustomizedView25599458800.png

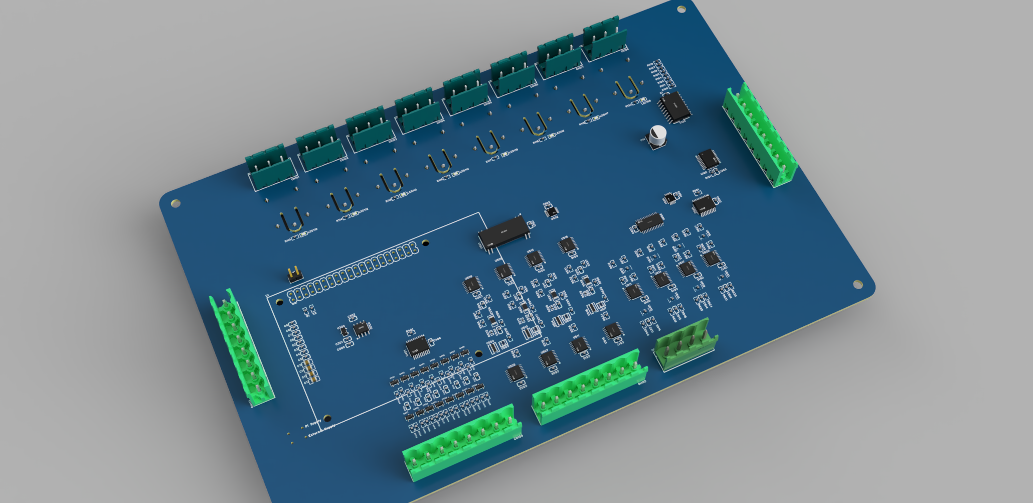
docs/Renderings/Board_v1_2025-Aug-29_05-47-25AM-000_CustomizedView25599458800.png
