edwardschmitz/sigcore-uc/docs/Renderings/Board_v1_2025-Aug-29_05-51-38AM-000_CustomizedView17774508226.png

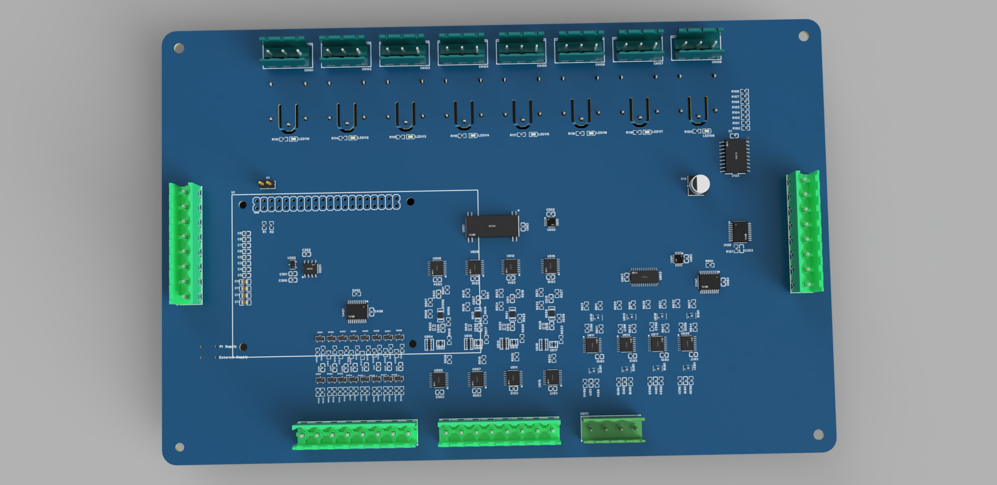
docs/Renderings/Board_v1_2025-Aug-29_05-51-38AM-000_CustomizedView17774508226.png
