edwardschmitz/sigcore-uc/docs/Renderings/Board_v1_2025-Aug-29_08-44-16PM-000_CustomizedView3914766899.png

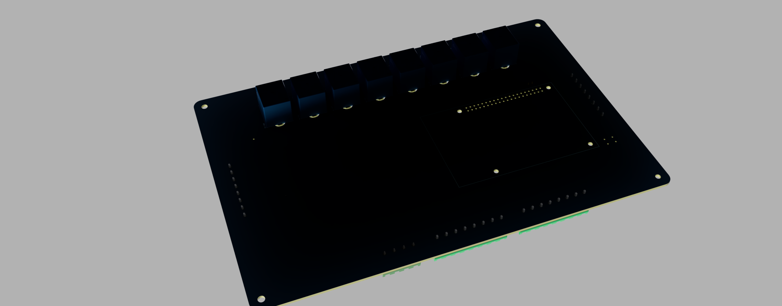
docs/Renderings/Board_v1_2025-Aug-29_08-44-16PM-000_CustomizedView3914766899.png
