edwardschmitz/sigcore-uc/docs/Renderings/Board_v1_2025-Aug-29_08-54-54PM-000_CustomizedView16152723619.png

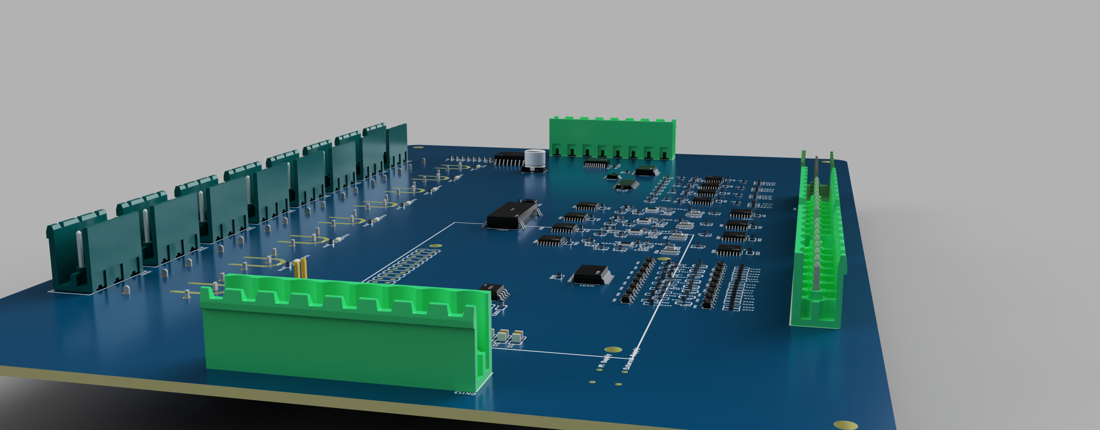
docs/Renderings/Board_v1_2025-Aug-29_08-54-54PM-000_CustomizedView16152723619.png
