edwardschmitz/sigcore-uc/docs/Renderings/Board_v1_2025-Aug-29_08-56-18PM-000_CustomizedView4115779644.png

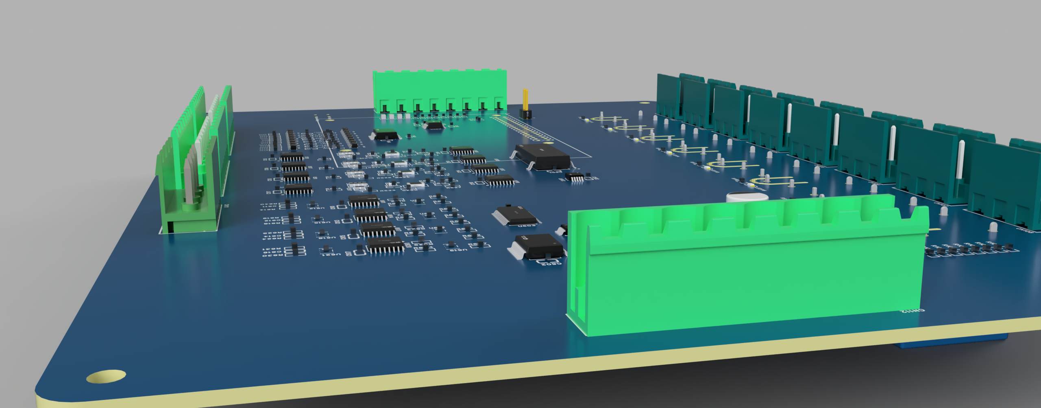
docs/Renderings/Board_v1_2025-Aug-29_08-56-18PM-000_CustomizedView4115779644.png
