edwardschmitz/sigcore-uc/docs/Renderings/Board_v1_2025-Aug-29_09-18-11PM-000_CustomizedView996420088.png

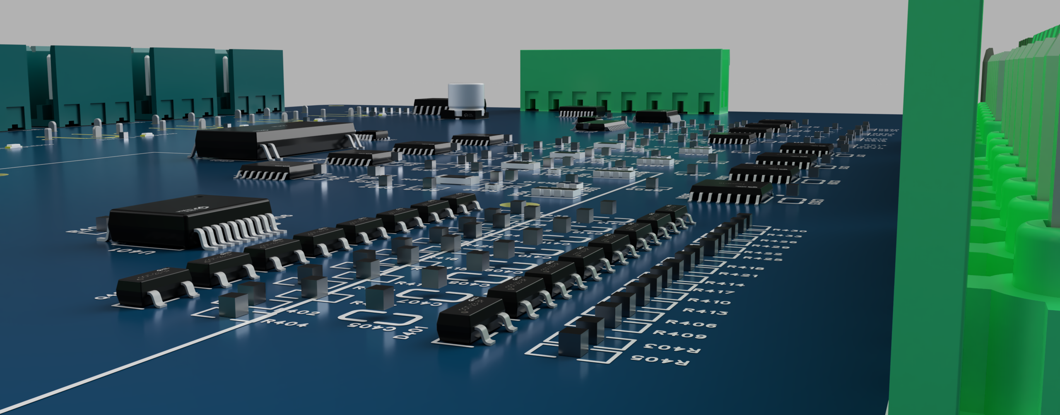
docs/Renderings/Board_v1_2025-Aug-29_09-18-11PM-000_CustomizedView996420088.png
