edwardschmitz/sigcore-uc/docs/Renderings/Board_v1_2025-Aug-30_12-17-42AM-000_CustomizedView750989842.png

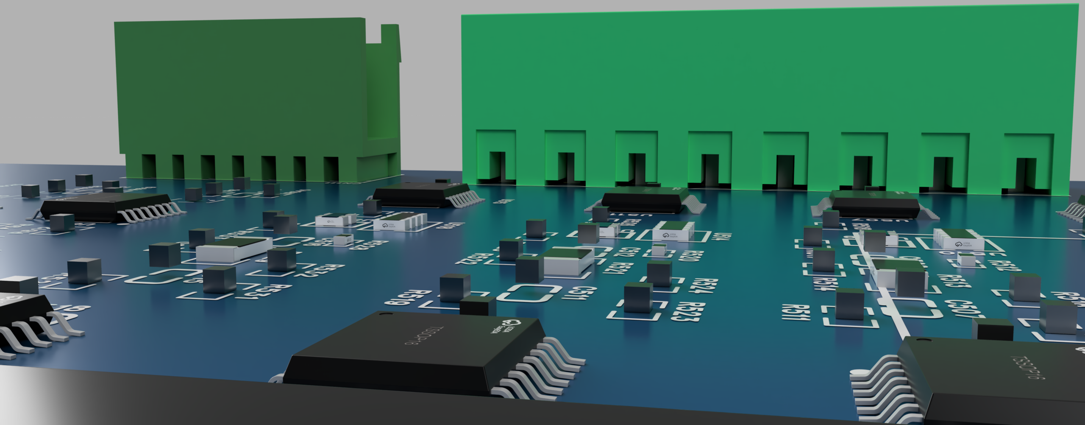
docs/Renderings/Board_v1_2025-Aug-30_12-17-42AM-000_CustomizedView750989842.png
