edwardschmitz/sigcore-uc/software/Web/Website/Website/root/images/AI1-0-10V-01.png

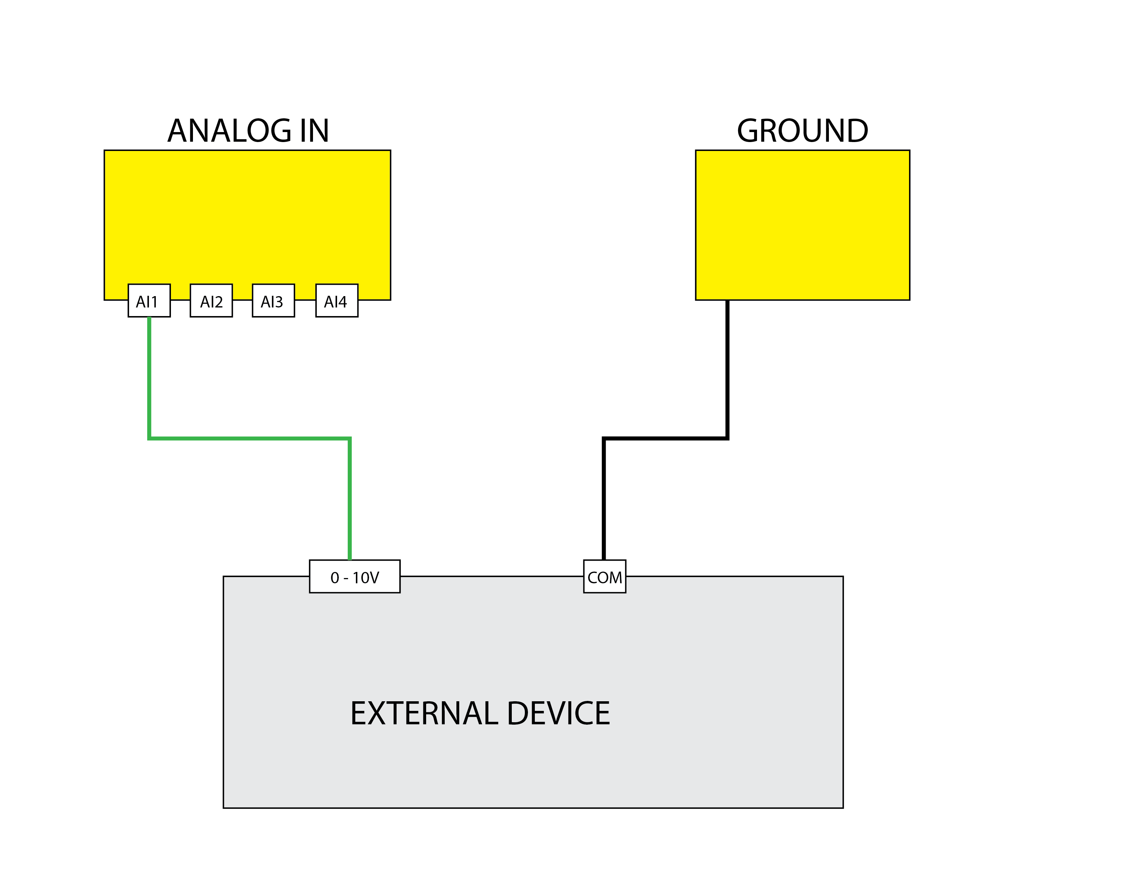
software/Web/Website/Website/root/images/AI1-0-10V-01.png
