edwardschmitz/sigcore-uc/software/Web/Website/Website/root/images/ai-assistant.jpg

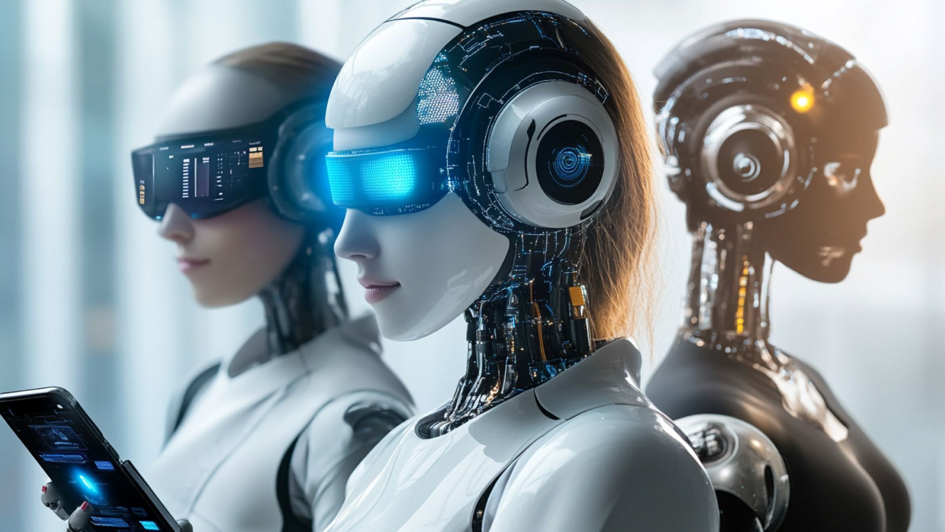
software/Web/Website/Website/root/images/ai-assistant.jpg
