edwardschmitz/sigcore-uc/software/Web/Website/Website/root/images/analog-input-properties.png

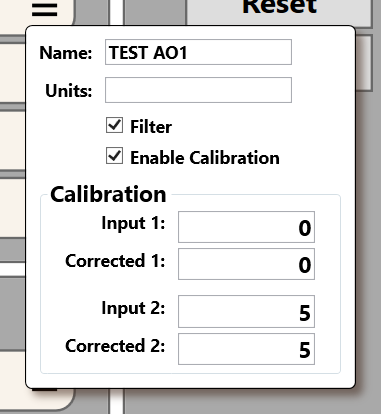
software/Web/Website/Website/root/images/analog-input-properties.png
