edwardschmitz/sigcore-uc/software/Web/Website/Website/root/images/analog-output-properties.png

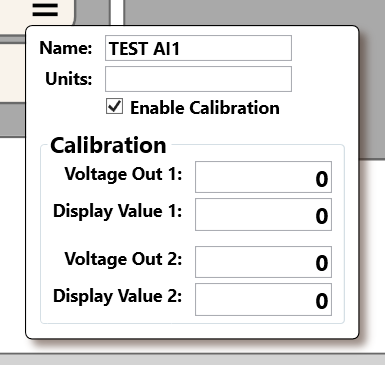
software/Web/Website/Website/root/images/analog-output-properties.png
