edwardschmitz/sigcore-uc/software/Web/Website/Website/root/images/Annotated.jpg

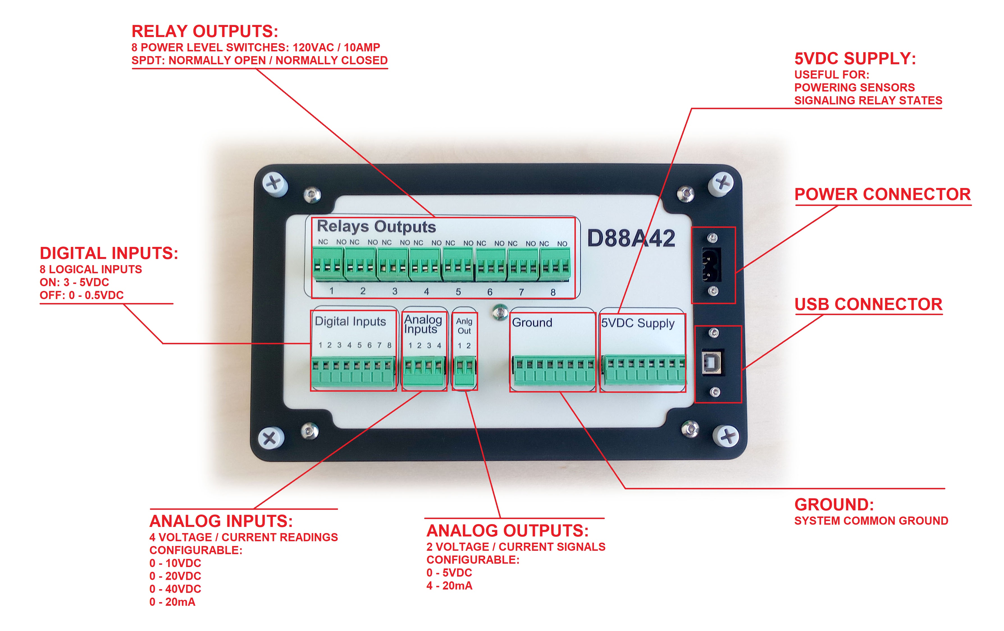
software/Web/Website/Website/root/images/Annotated.jpg
