edwardschmitz/sigcore-uc/software/Web/Website/Website/root/images/Circuit.png

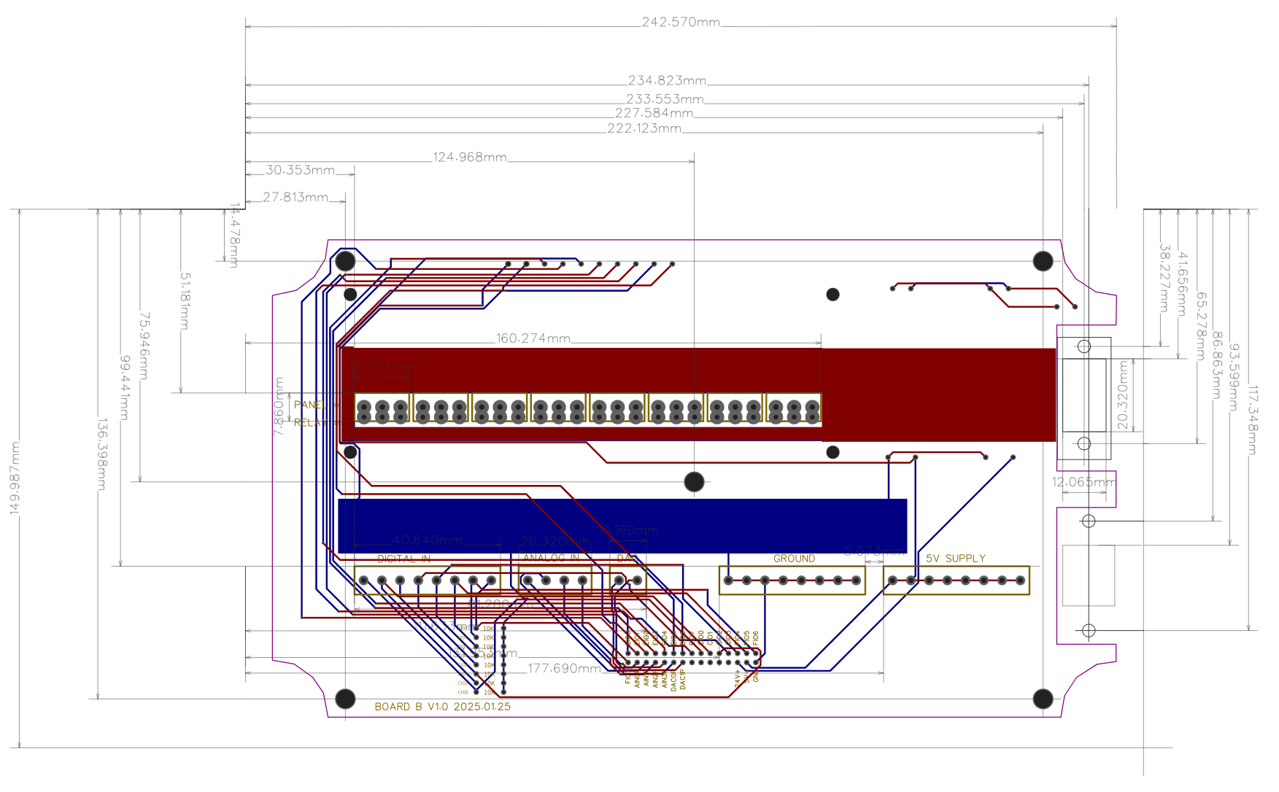
software/Web/Website/Website/root/images/Circuit.png
