edwardschmitz/sigcore-uc/software/Web/Website/Website/root/images/connection-screen.png

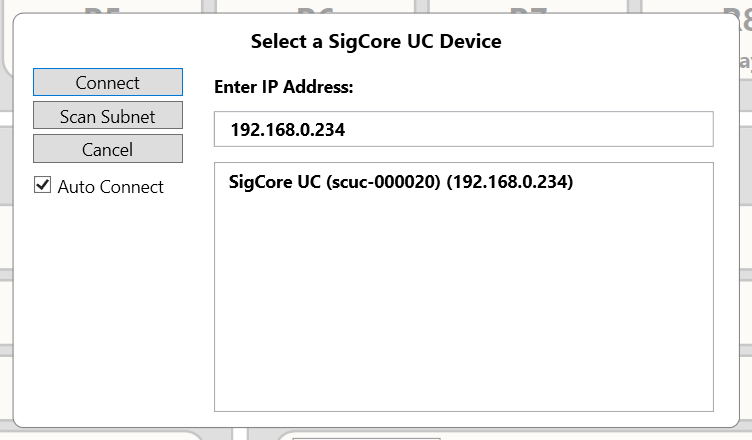
software/Web/Website/Website/root/images/connection-screen.png
