edwardschmitz/sigcore-uc/software/Web/Website/Website/root/images/dotnet-software.jpg

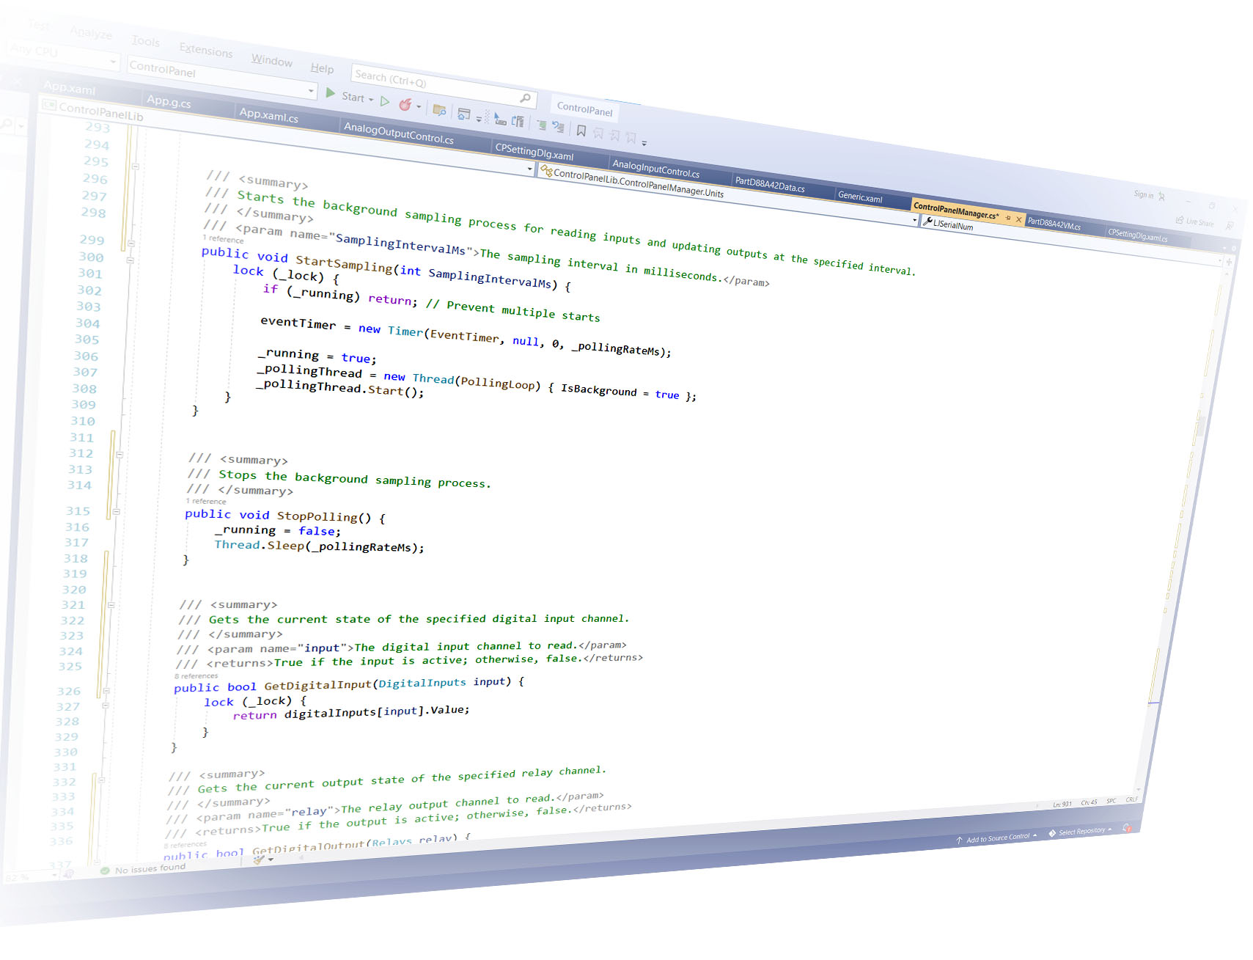
software/Web/Website/Website/root/images/dotnet-software.jpg
