edwardschmitz/sigcore-uc/software/Web/Website/Website/root/images/LidAnalogIn.png

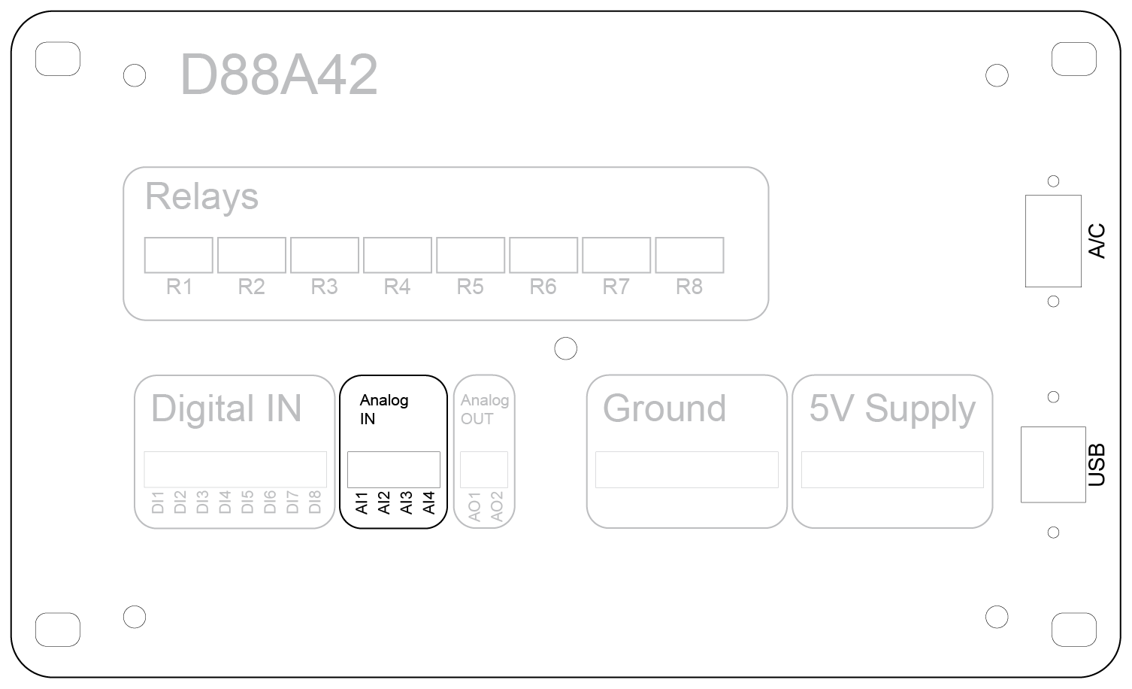
software/Web/Website/Website/root/images/LidAnalogIn.png
