edwardschmitz/sigcore-uc/software/Web/Website/Website/root/images/LidDigitalIn.png

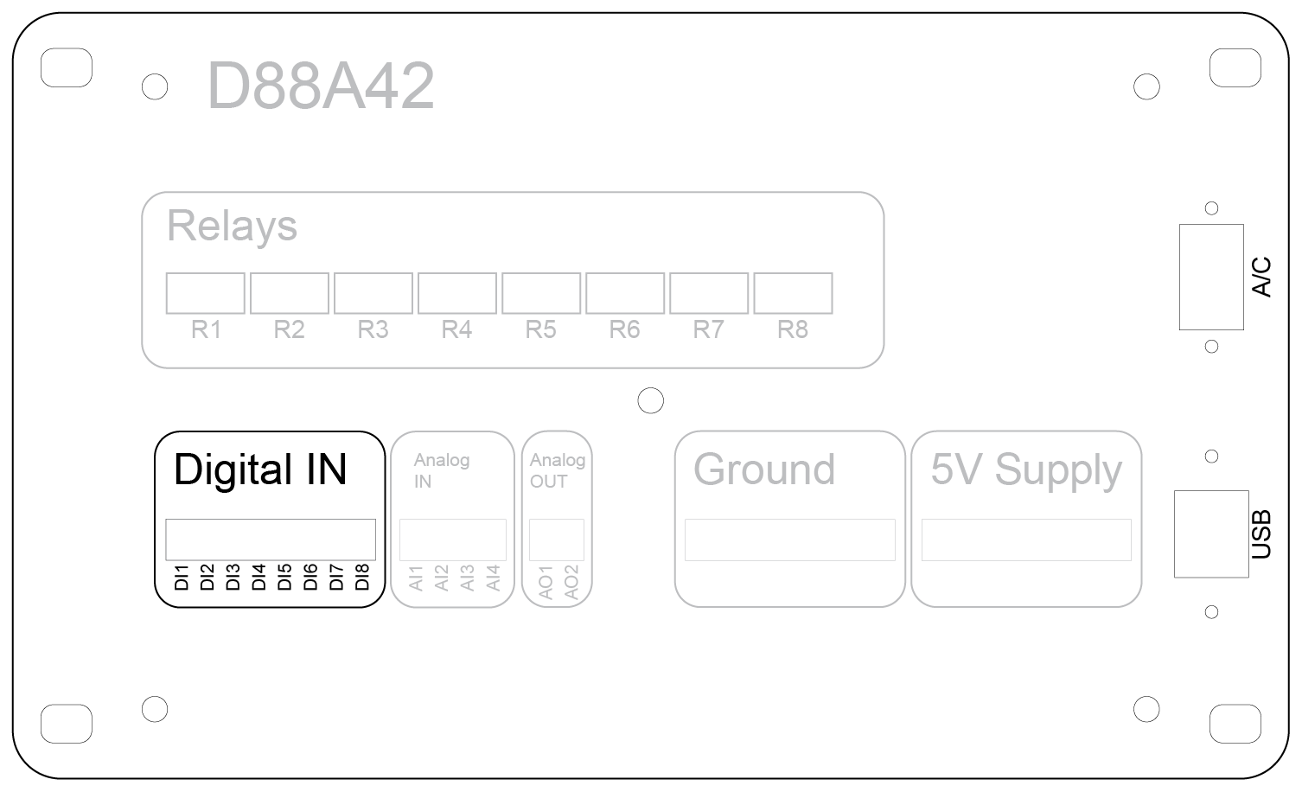
software/Web/Website/Website/root/images/LidDigitalIn.png
