edwardschmitz/sigcore-uc/software/Web/Website/Website/root/images/LidRelay.png

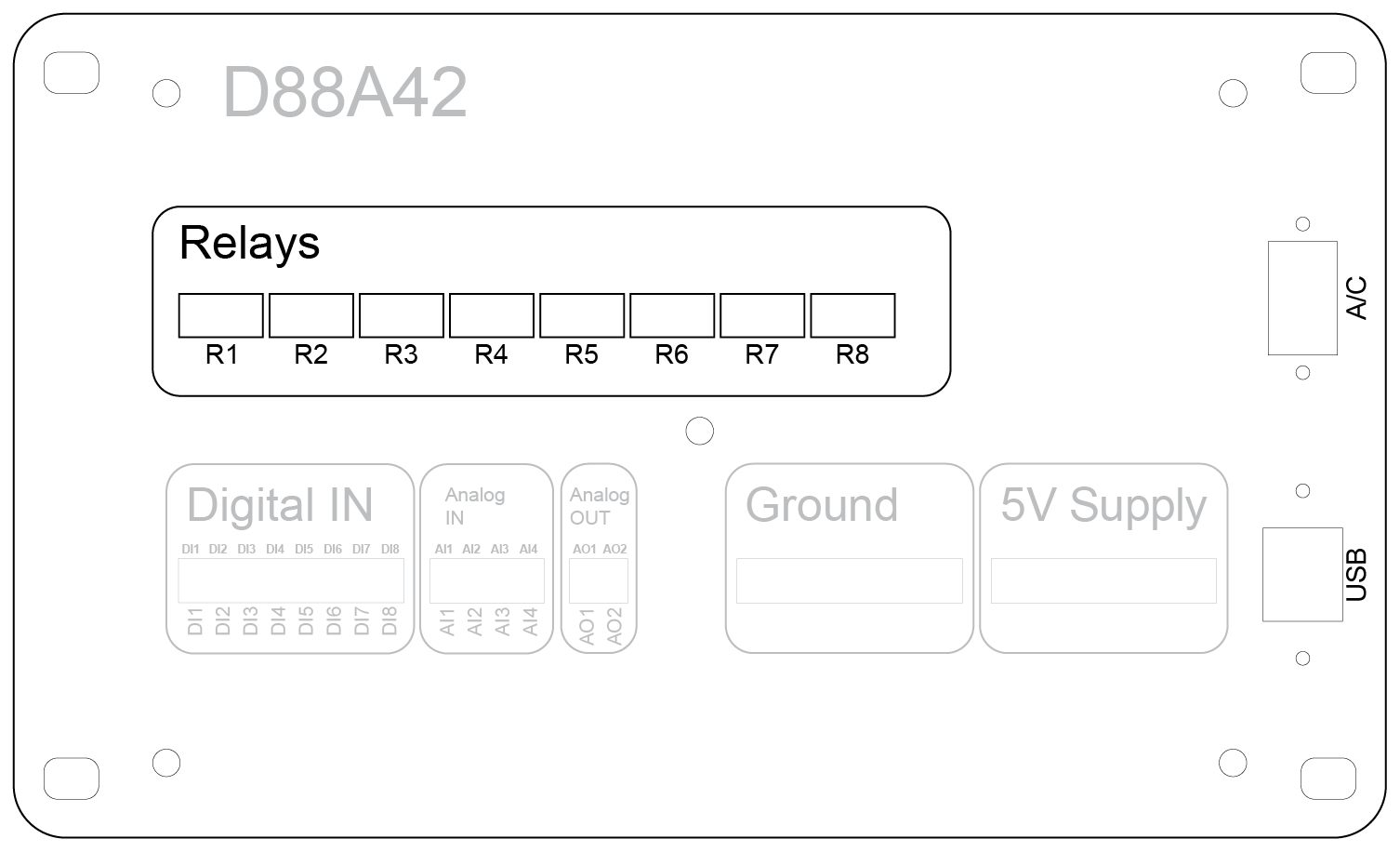
software/Web/Website/Website/root/images/LidRelay.png
