edwardschmitz/sigcore-uc/software/Web/Website/Website/root/images/PID-config.png

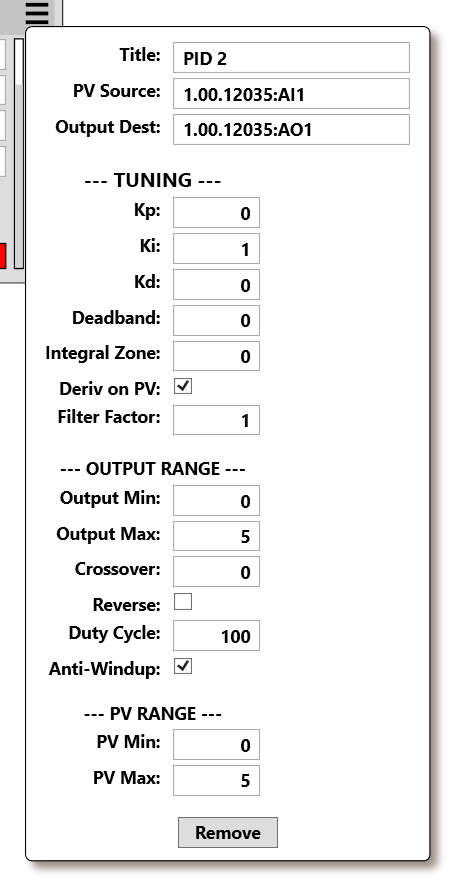
software/Web/Website/Website/root/images/PID-config.png
