edwardschmitz/sigcore-uc/software/Web/Website/Website/root/images/PID.png

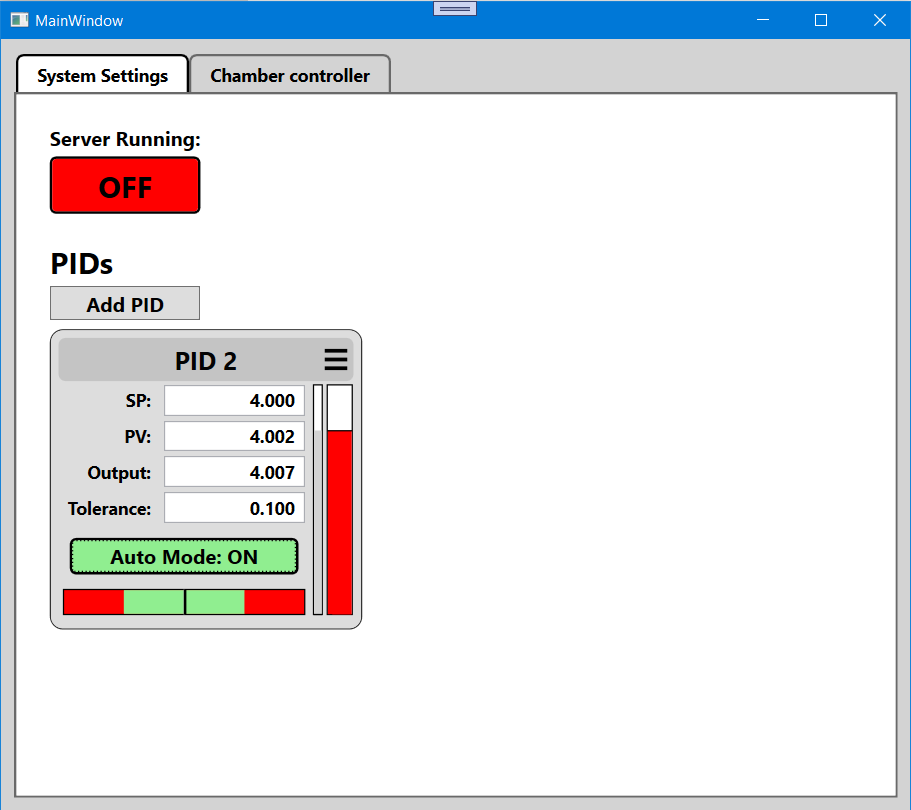
software/Web/Website/Website/root/images/PID.png
