edwardschmitz/sigcore-uc/software/Web/Website/Website/root/images/python.png

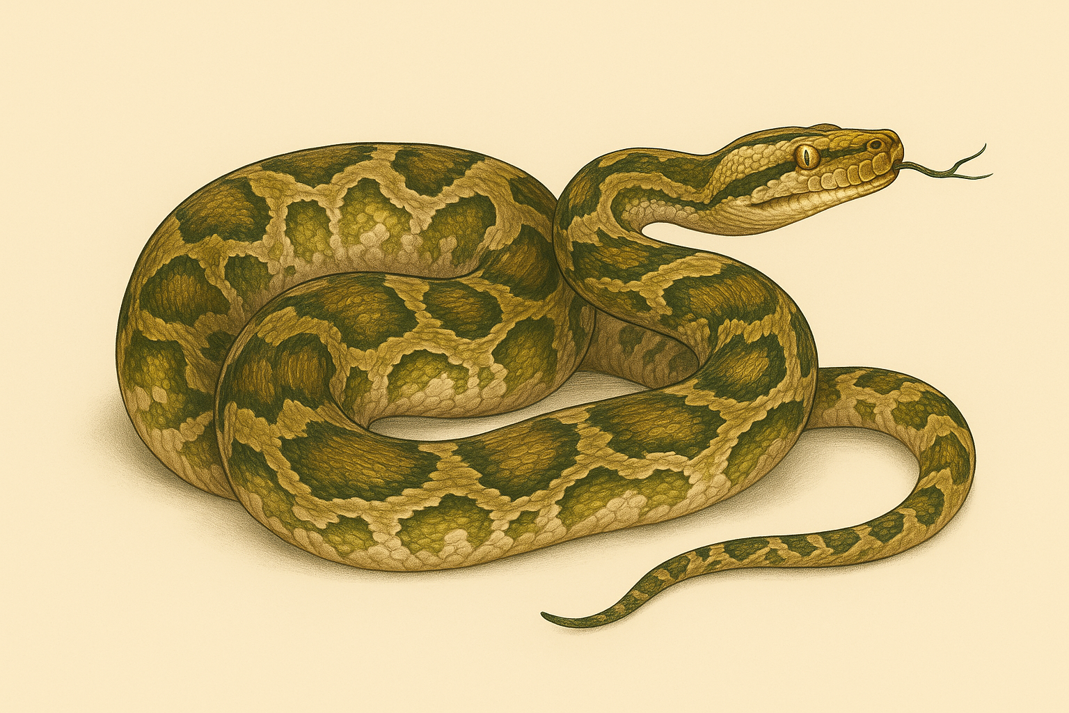
software/Web/Website/Website/root/images/python.png
