edwardschmitz/sigcore-uc/software/Web/Website/Website/root/images/Relay-5VDC Start Stop.png

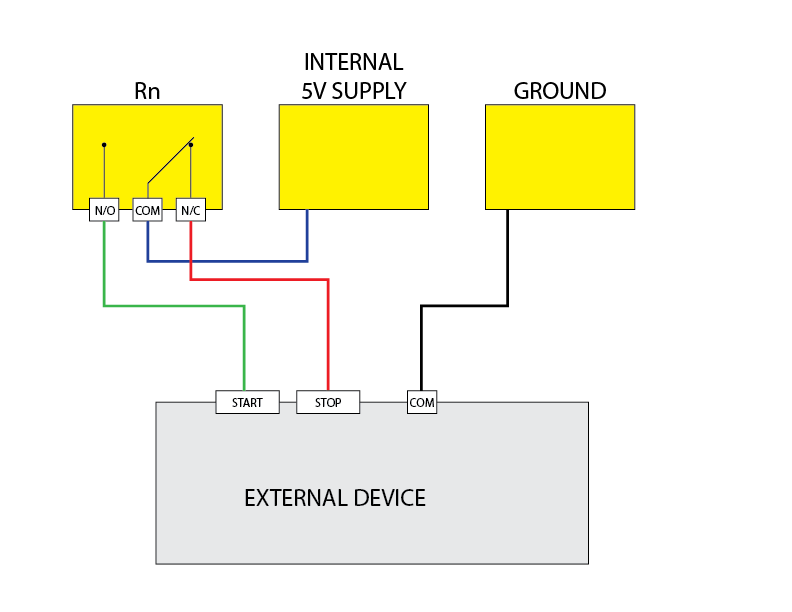
software/Web/Website/Website/root/images/Relay-5VDC Start Stop.png
