edwardschmitz/sigcore-uc/software/Web/Website/Website/root/images/Relay-5VDC.png

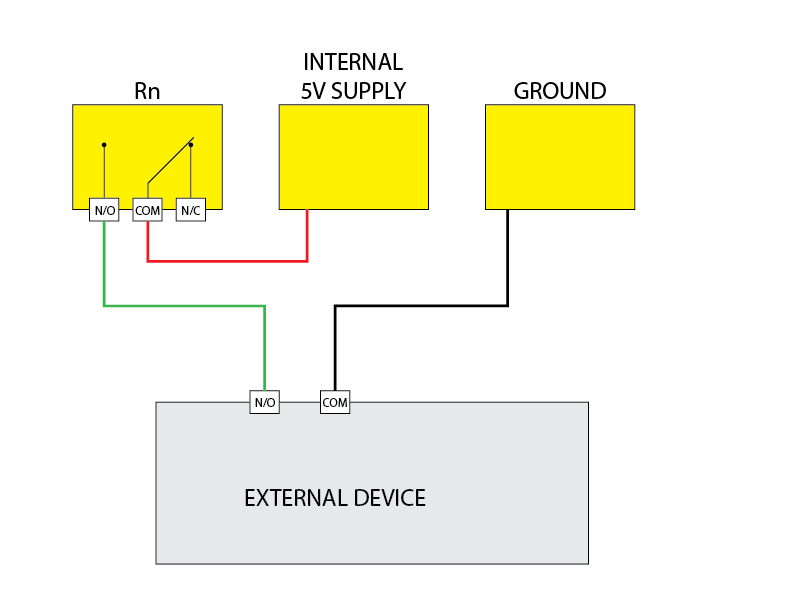
software/Web/Website/Website/root/images/Relay-5VDC.png
