edwardschmitz/sigcore-uc/software/Web/Website/Website/root/images/Relay-24VDC.png

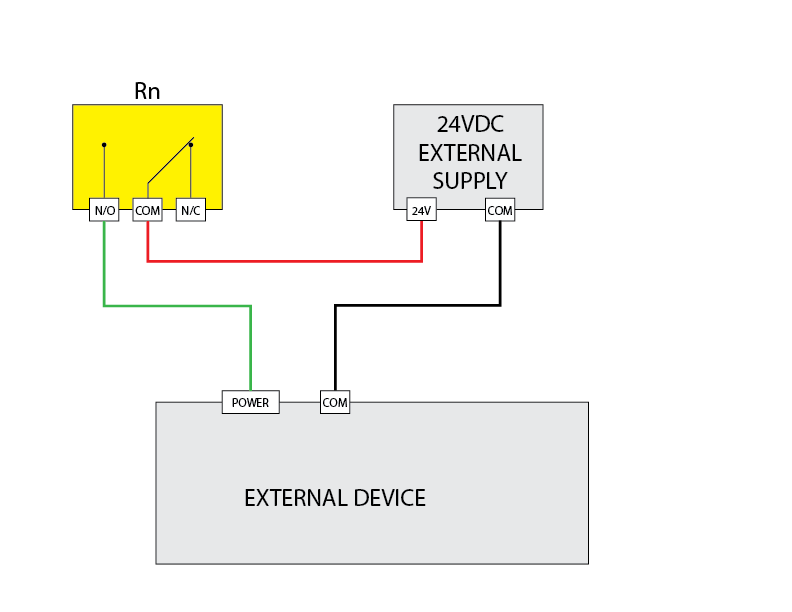
software/Web/Website/Website/root/images/Relay-24VDC.png
