edwardschmitz/sigcore-uc/software/Web/Website/Website/root/images/Relay-Close Contact.png

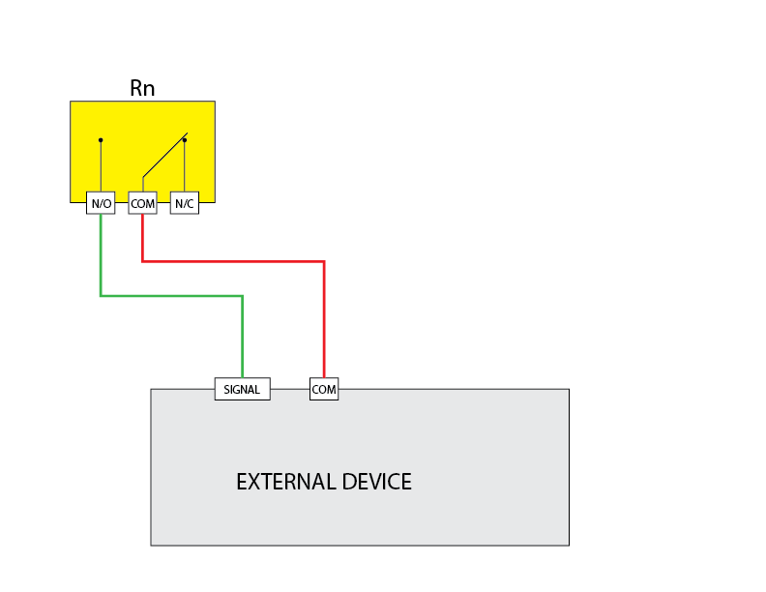
software/Web/Website/Website/root/images/Relay-Close Contact.png
