edwardschmitz/sigcore-uc/software/Web/Website/Website/root/images/settings.png

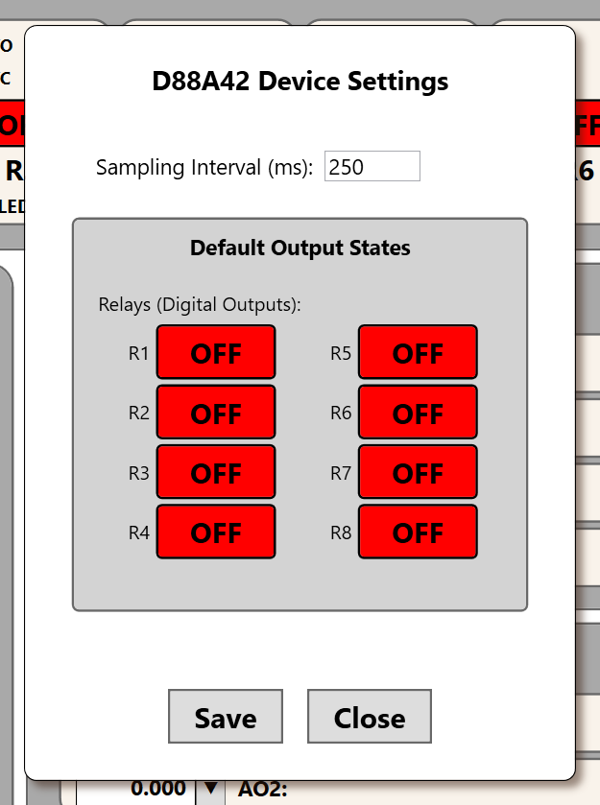
software/Web/Website/Website/root/images/settings.png
