edwardschmitz/sigcore-uc/software/Web/Website/Website/root/images/smartscreen-warning.png

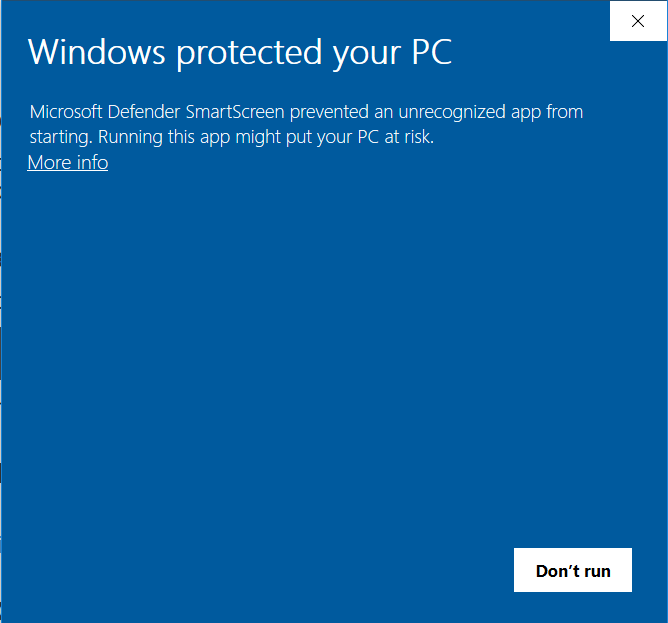
software/Web/Website/Website/root/images/smartscreen-warning.png
