edwardschmitz/sigcore-uc/software/Web/Website/Website/root/images/software.png

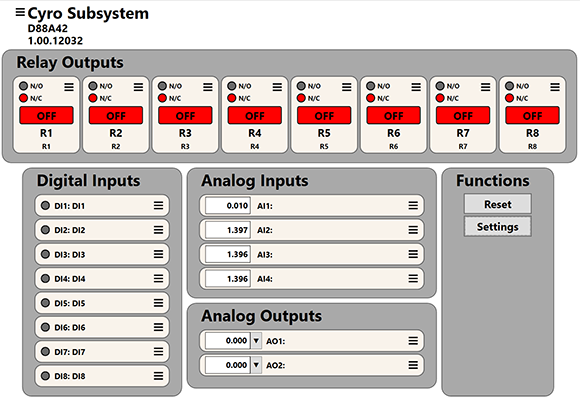
software/Web/Website/Website/root/images/software.png
