edwardschmitz/sigcore-uc/software/Web/Website/Website/root/images/purchase.png

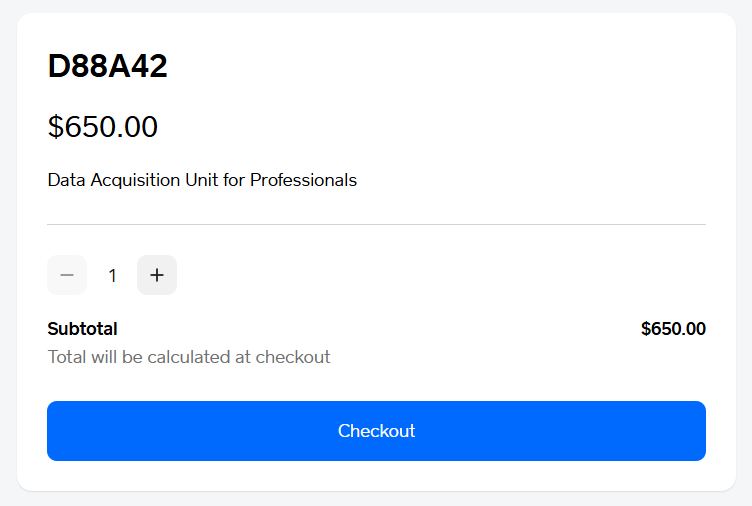
software/Web/Website/Website/root/images/purchase.png
