edwardschmitz/sigcore-uc/docs/Drawings/sketches/real-world-setup.png

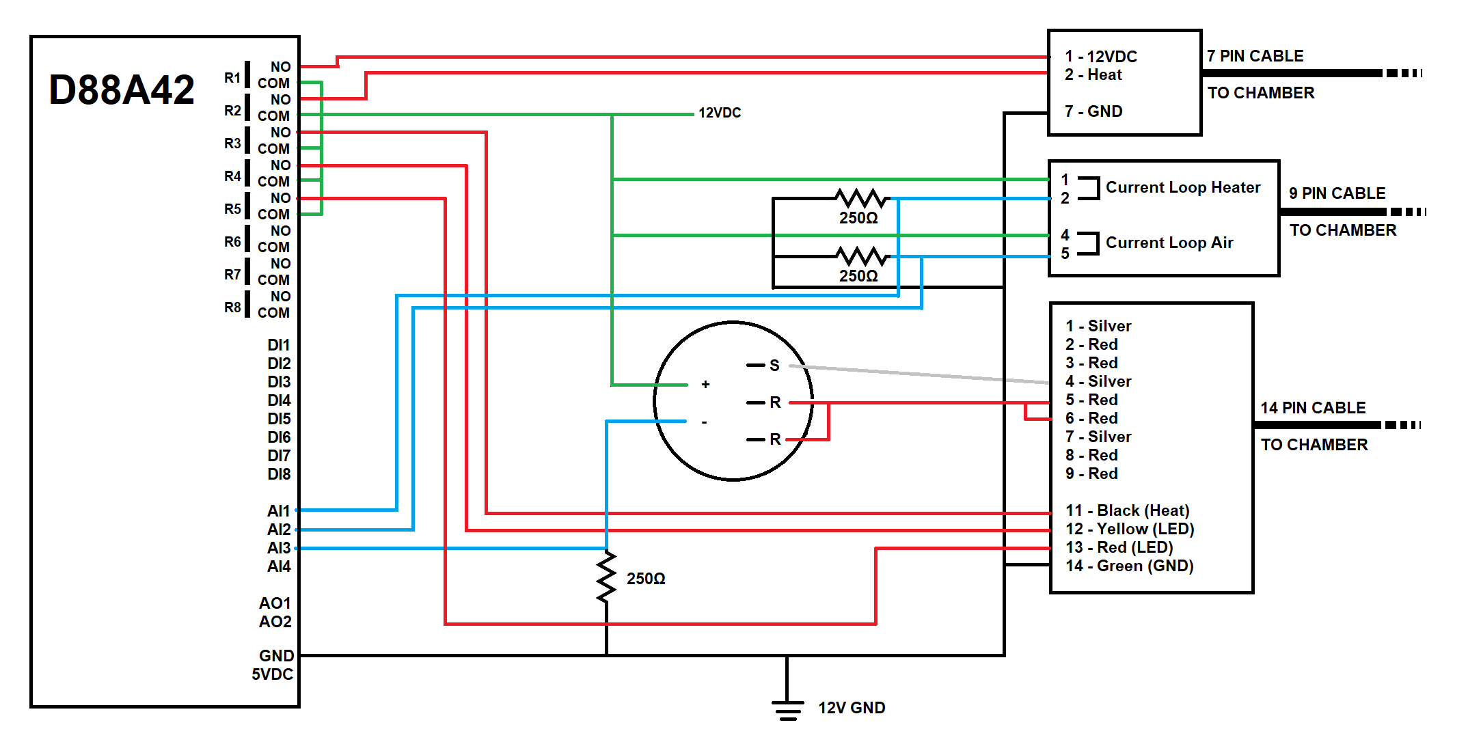
docs/Drawings/sketches/real-world-setup.png
