edwardschmitz/sigcore-uc/software/Web/Website/Website/root/images/DIUsage01.png

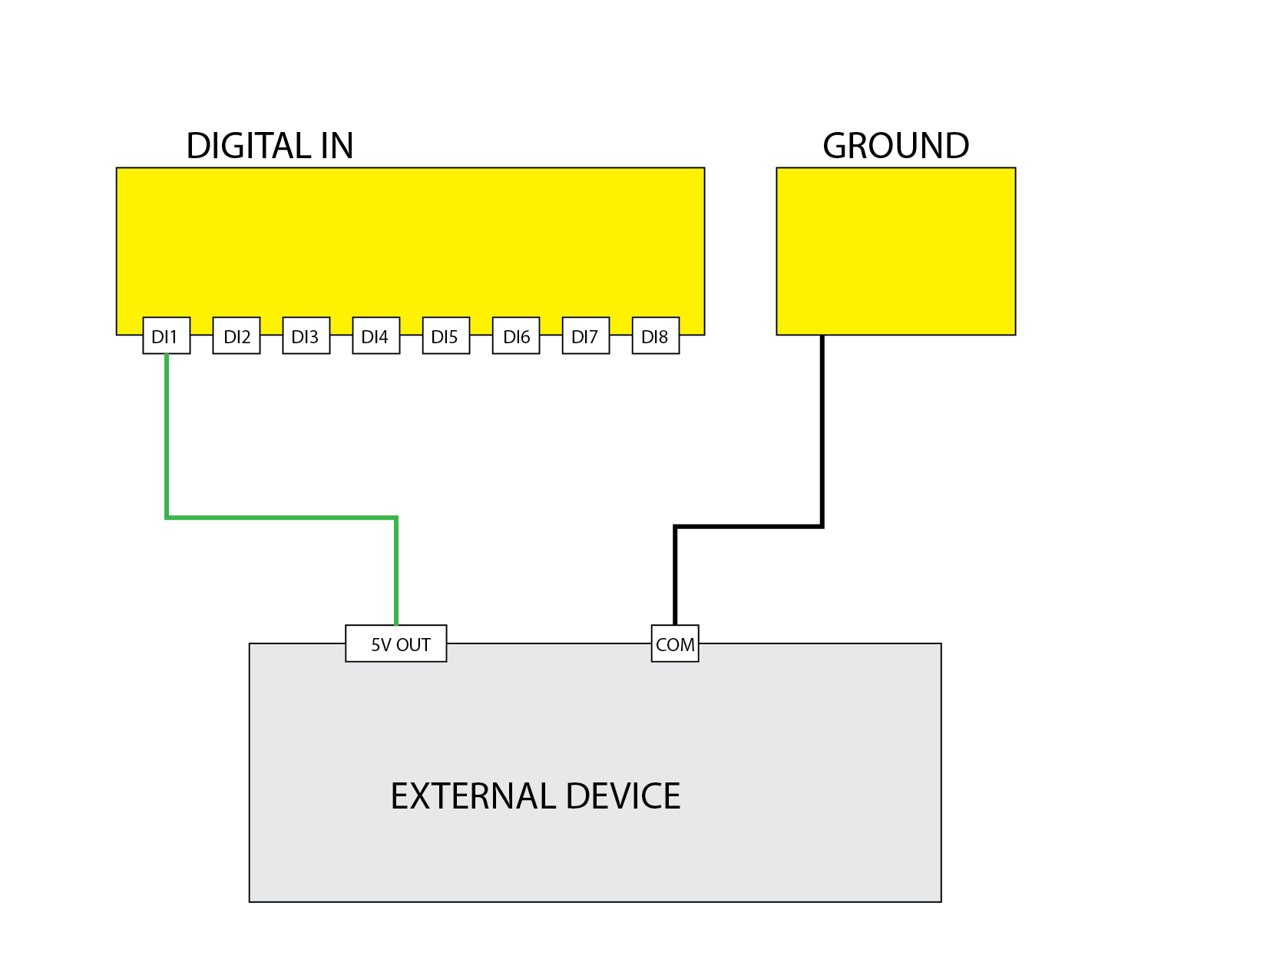
software/Web/Website/Website/root/images/DIUsage01.png
