edwardschmitz/sigcore-uc/software/Web/Website/Website/root/images/DIUsage02.png

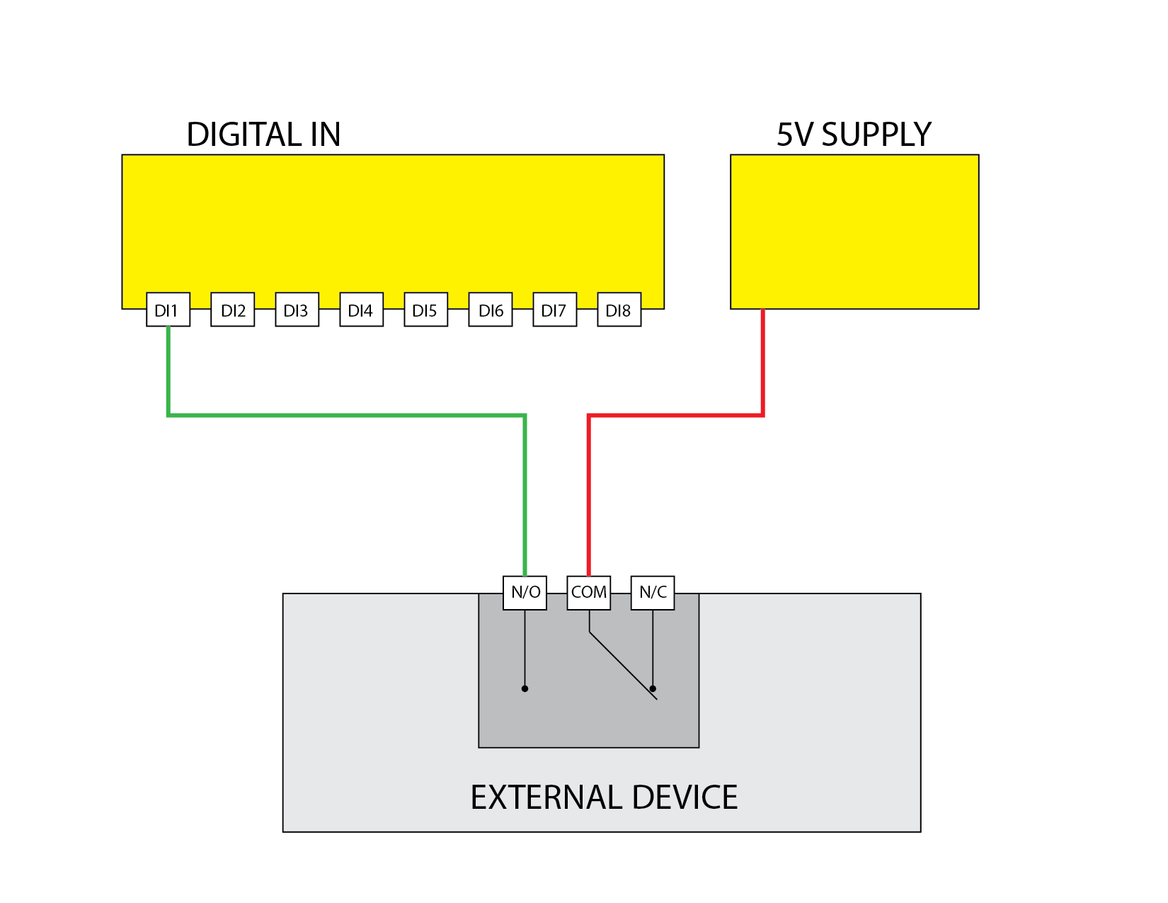
software/Web/Website/Website/root/images/DIUsage02.png
