edwardschmitz/sigcore-uc/hardware/Review/SMT025090962540_T_20250915064154.jpg

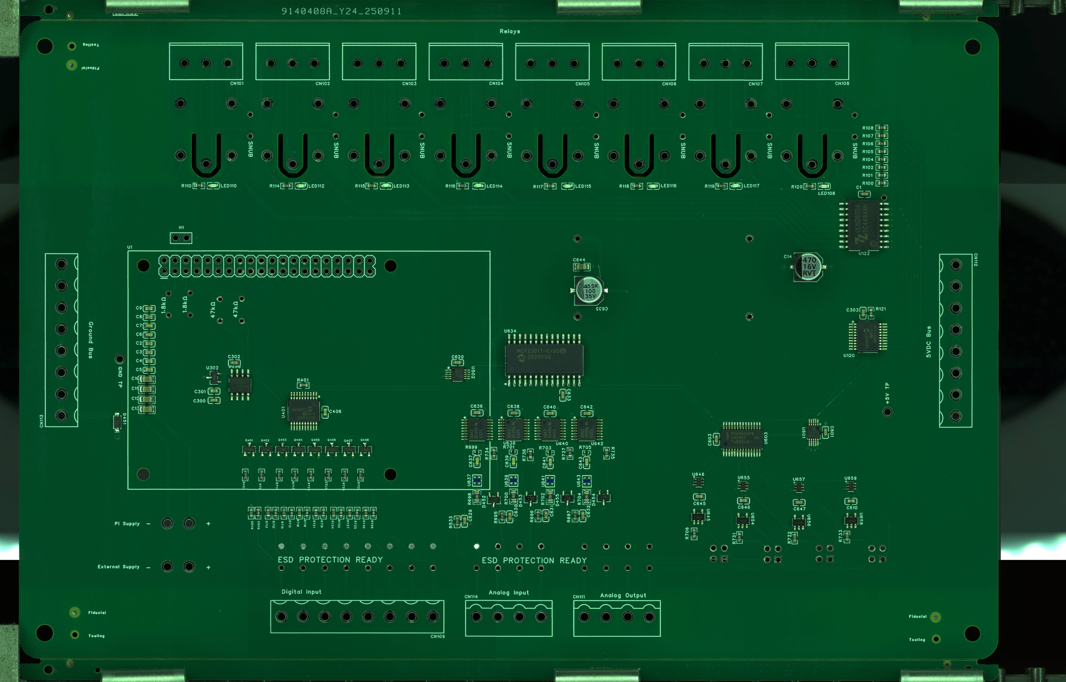
hardware/Review/SMT025090962540_T_20250915064154.jpg
